s-katada/kobu/case/stl/main-unit/main-side-plate.stl

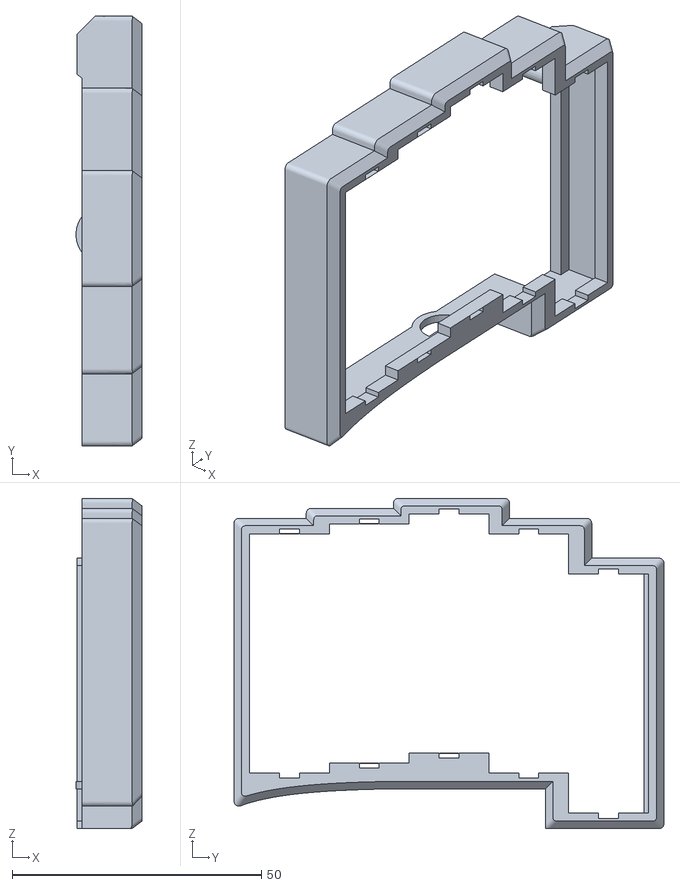
[picture p15: CAD file, 2026-05-27, an earlier design]
case/stl/main-unit/main-side-plate.stl
13.2 x 86.3 x 66.3
