s-katada/kobu/v1/case/3mf/08-main-top-plate.3mf

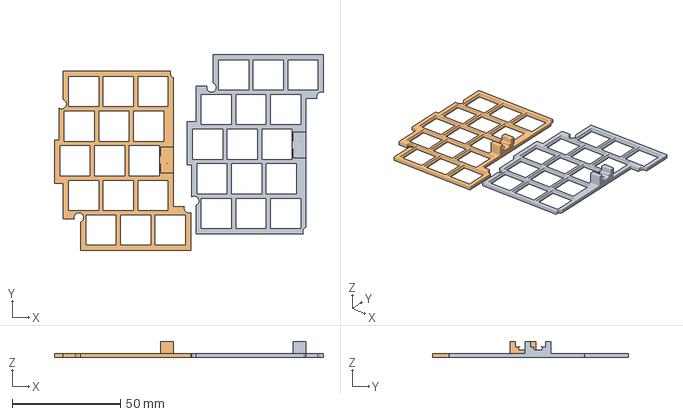
[picture p16: CAD file, 2026-07-02, an earlier design]
v1/case/3mf/08-main-top-plate.3mf
124.3 x 90.7 x 7.50 mm
main-top-plate-v1.stl x 2
