s-katada/kobu/v1/case/stl/main-unit/main-unit-left-spacer-top.stl

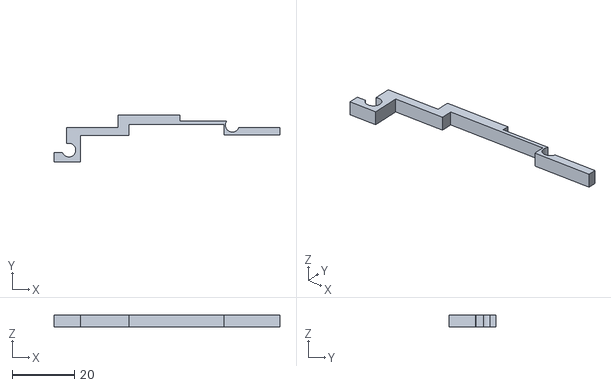
[picture p17: CAD file, 2026-07-02, an earlier design]
v1/case/stl/main-unit/main-unit-left-spacer-top.stl
72.5 x 15.1 x 3.90
