s-katada/kobu/v1/pcb/dxf/main-unit.dxf

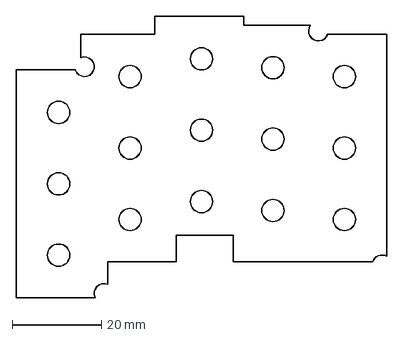
[picture p18: CAD file, 2026-07-02, an earlier design]
v1/pcb/dxf/main-unit.dxf
83.0 x 63.0 mm
