s-katada/kobu/v2/firmware/rmk/build.rs

use const_gen::*;
use std::fs::File;
use std::io::{Read, Write};
use std::path::{Path, PathBuf};
use std::{env, fs};
use xz2::read::XzEncoder;

fn main() {
    println!("cargo:rerun-if-changed=vial.json");
    println!("cargo:rerun-if-changed=keyboard.toml");

    patch_rmk_ble_for_macos();
    patch_rmk_battery_service();
    patch_rmk_battery_processor_signal();
    patch_rmk_battery_kobu_atomics();
    patch_rmk_kobu_settings_atomics();
    patch_rmk_via_custom_get_kobu();
    // NOTE: peripheral_bootloader_jump must run BEFORE via_custom_set_kobu_settings:
    // the latter anchors on the CustomSetValue arm AFTER the bootloader-jump patch
    // has rewritten the upstream stub. (Order only matters on a pristine registry —
    // e.g. a clean cargo cache or CI — because the patches are marker-idempotent.)
    patch_rmk_peripheral_bootloader_jump();
    patch_rmk_via_custom_set_kobu_settings();
    patch_rmk_via_custom_save_kobu();
    patch_rmk_macro_adc_acquisition_time();
    patch_rmk_host_advertise_fast();
    patch_rmk_split_peripheral_advertise_fast();
    patch_rmk_split_peripheral_wake_on_pointer();
    patch_rmk_split_peripheral_publish_battery();
    patch_rmk_split_peripheral_decode_battery_while_advertising();
    patch_rmk_conn_params_fast_settling();
    patch_rmk_host_conn_low_latency();
    patch_rmk_split_conn_low_latency();
    patch_rmk_split_conn_event_length();
    patch_rmk_split_conn_event_min_reservation();
    patch_rmk_split_conn_offbeat_interval();
    patch_rmk_macro_sdc_buffers();
    patch_rmk_flow_tap_exempt_language();
    patch_rmk_flow_tap_exempt_language_held();
    patch_rmk_split_state_resync_fast();
    patch_rmk_force_ble_conn_type();
    patch_rmk_force_hid_cccd_on_connect();
    patch_rmk_gate_ble_writer_on_encrypted();
    patch_rmk_timeout_ble_writer();
    patch_rmk_request_security_on_connect();
    patch_rmk_keymap_layer_pub();
    patch_rmk_last_key_tick_atomic();
    patch_rmk_record_last_key_tick();
    // Round 7 — boot-trackball BLE wedge + mouse-drag/copy. These add NEW
    // atomics and NEW rmk patches, so a `cargo clean --release -p rmk` is
    // required once after pulling this change (see the buildrs-patch-recompile
    // note in project memory). The atomics injection MUST run before the
    // patches that reference the atomics by path are compiled, but ordering
    // among build.rs functions only matters for anchor availability — so the
    // atomics patch anchors on the last-key-tick atomic injected just above.
    patch_rmk_kobu_wedge_drag_atomics();
    patch_rmk_set_host_connected();
    patch_rmk_timeout_split_writes();
    patch_rmk_capture_mouse_buttons();
    patch_rmk_pmw3610_slower_poll();
    // Round 8 — the boot-trackball wedge (R1–R7 all failed). Root cause: the
    // peripheral forwards every pointer sample over the split link with an
    // UNBOUNDED blocking write (split/peripheral.rs), flooding the central's
    // single shared trouBLE RX pool during the Mac SMP/encryption window and
    // silently dropping the encryption PDU → "connected but dead until a
    // supervision-timeout reconnect." Fix: bound that forward (Layer A) AND gate
    // the whole PMW3610 pipeline on BOTH halves until the host link is READY
    // (BLE-encrypted OR USB) — Layer B. Adds new atomics + a new SplitMessage
    // variant; REQUIRES `cargo clean --release -p rmk` (registry-patch gotcha).
    patch_rmk_kobu_input_gate_atomics();
    patch_rmk_timeout_peripheral_event_write();
    patch_rmk_pmw3610_input_gate();
    // Round 7 ball-diag atomics: must run before the two patches below, which
    // reference them (KOBU_BALL_FF_REJECTS / KOBU_BALL_INIT_READY).
    patch_rmk_kobu_ball_diag_atomics();
    // PMW3610 boot-lottery fix: the stock driver gives up after 3 init
    // attempts (~300 ms) and parks dead until power-cycle, and treats a
    // flaky-SPI all-0xff burst read as a real (phantom) motion sample.
    // Retry init forever (fast then relaxed backoff) and reject 0xff frames.
    patch_rmk_pmw3610_init_retry_forever();
    patch_rmk_pmw3610_reject_ff_frame();
    // Round 7 — scroll-death recurrence, no self-heal: a torn bit-banged SPI
    // config write (preempted mid-byte by MPSL radio interrupts) can leave
    // the sensor misconfigured but still Ready. Verify-and-retry the writes.
    patch_rmk_pmw3610_verify_init_writes();
    // Round 8 — live-confirmed (led-ball-diag): init retries fail while the
    // radio is busy, succeeding only in quiet moments. Run the one-time init
    // BEFORE the input gate (power-on is the reliably radio-quiet window).
    patch_rmk_pmw3610_early_init();
    // KOBU: patch_rmk_bitbang_atomic_bytes REVERTED 2026-07-15 (round 9) — a
    // mid-session central reboot (LED green/blue -> solid RED with scroll
    // dead, right ball fine; init_state can only reach that state via a
    // fresh boot + persistently-failing re-init) is suspected to be MPSL
    // tripping its interrupt-latency assert on the repeated ~30 µs PRIMASK
    // masks (7-byte bursts every 8 ms poll = constant masking). It also
    // couldn't protect the preemptible inter-byte Timer::after gaps, so it
    // was an incomplete fix regardless. Do NOT re-add without addressing
    // both: a latency budget that satisfies MPSL, and inter-byte coverage.
    patch_rmk_split_host_ready_variant();
    patch_rmk_emit_host_ready();
    patch_rmk_peripheral_apply_host_ready();
    // Round 10 — the wedge is a HANG (not reset) on the BONDED-RECONNECT-while-
    // Mac-holds-a-STALE-link path + trackball motion. On a stale resume the Mac
    // re-encrypts from the stored LTK and fires a dense GATT cache-revalidation
    // burst; kobu opened the trackball gate on the first encrypted GATT read
    // (R8), i.e. straight into that burst, BEFORE host TX credits were flowing —
    // the ~500Hz pointer flood then starved the single shared trouBLE TX queue +
    // 16-packet pool, the lone TxRunner parked on a host PDU, and the UNBOUNDED
    // `reply.send().await` in gatt_events_task deadlocked. Layer A bounds that
    // await; Layer C shrinks the stale window (5s->2s) like ZMK/KobitoKey.
    // (Layer B = a 2s post-encryption settle in run_input_gate_central, firmware;
    //  Layer D = bigger trouBLE pool via .cargo/config.toml env.)
    patch_rmk_timeout_gatt_reply();
    patch_rmk_supervision_timeout_2s();
    // Pointer "もっさり over time": macOS relaxes the bonded HID link to a slow
    // interval (~30-50ms) for power-saving after a while; rmk only logs the
    // change, so the pointer report rate drifts to ~20-33Hz and STAYS there
    // until reconnect. Capture the live interval and re-assert the fast 7.5ms
    // params, but only when actually drifted slow (don't spam macOS).
    patch_rmk_host_conn_interval_atomic();
    patch_rmk_reassert_fast_conn_params();
    // Round 12: make the round-11 re-assert EVENT-DRIVEN. After a motion-heavy
    // stale reconnect macOS lands the link fully relaxed (~30-50ms); the 10s
    // poll then took up to ~10s to pull it back to 7.5ms = the acute "もっさり→
    // しばらくで回復". Signal the re-assert loop the instant a slow interval lands
    // (in the ConnectionParamsUpdated arm) + keep a 2s backstop, collapsing the
    // recovery from ~10s to ms. Anchors on the round-11 patched text → run after.
    patch_rmk_conn_drift_atomic();
    patch_rmk_conn_drift_event_driven();
    // Round 18 — pointer もっさり OVER TIME = the macOS host link relaxes over a
    // session. kobu's stage-2 request was a FIXED min==max=7.5ms, BELOW Apple's
    // ~11.25ms BLE-HID floor → macOS SILENTLY REJECTS it → the link sits at
    // stage-1's fixed 15ms (66Hz, never the 7.5ms/133Hz ZMK reaches) and over
    // time relaxes into the 15-18ms band that the >18ms re-assert gate never
    // corrects. ZMK requests a RANGE 7.5-15ms (MIN_INT=6/MAX_INT=12) which macOS
    // CAN satisfy near its floor and HOLDS all session. This patch makes kobu
    // ZMK-faithful: stage-2 → range 7.5-15ms, re-assert → range 7.5-15ms, both
    // drift gates 18ms→12ms (close the dead band; matches the "past 12ms"
    // comment). ADDITIVE — anchors on the reassert/conn-drift patched text, so
    // it MUST run after them. Host-only + request-not-force → no wedge risk.
    patch_rmk_host_conn_range_zmk();
    // Round 19 — residual over-time excursions: macOS grants the MAX end of the
    // requested range, so round-18's [7.5,15ms] rested at 15ms (66Hz) and 15ms
    // ALSO tripped the >12ms gate (self-sustained re-assert churn that re-opens
    // negotiation → macOS re-grants the slow end). ZMK requests its range ONCE
    // and never perturbs it. Cap MAX at the 11.25ms Apple HID floor (rest
    // 89-133Hz) + raise the gate 12ms→13ms so the healthy point stops re-tripping
    // (a true relax ≥30ms still fires). ADDITIVE on the round-18 output → after.
    patch_rmk_host_conn_narrow_max_r19();
    // Round 21 — pointer のろのろ ROOT CAUSE (LED-confirmed: PURPLE ~15ms during
    // のろのろ, no white): peripheral LATENCY, not interval. kobu requested
    // max_latency=0 at every host conn-param site; ZMK requests latency=30.
    // latency=0 forbids macOS the cheap power-save (skip idle intervals), so its
    // ONLY lever is to RELAX THE INTERVAL (~15ms=66Hz=のろのろ); the 2s re-assert
    // then claws it back = the ~5s relax/recover loop. latency=30 keeps the fast
    // interval and lets macOS skip idle events instead (ZMK behaviour). Host conn
    // only (the split link in split/ble/central.rs stays latency 0 — low relay
    // lag). Active input is instant (latency applies only when idle).
    patch_rmk_host_latency_30_r21();
    // Round 23 diagnostic — count pointer samples PRODUCED by the PMW3610 (in
    // read_event) so the PERIPHERAL LED can show its own production rate. The
    // central LED already shows the ARRIVAL rate; comparing the two decisively
    // separates "right sensor produces too few" (production) from "split link
    // loses them in transit". Two additive patches (atomic + increment).
    patch_rmk_peripheral_samples_atomic_r23();
    patch_rmk_peripheral_samples_count_r23();
    // Round 24 — のろのろ ROOT CAUSE (confirmed: both diag LEDs green during のろのろ
    // ⇒ samples reach the central fine; host link is the issue; "~5s recovery" =
    // kobu's 2s re-assert cycle). kobu RE-ASSERTS host conn-params every 2s
    // (churn), which re-opens negotiation and makes macOS RELAX the link →
    // のろのろ → re-assert claws back in ~5s → relaxes again. KobitoKey requests
    // host params ONCE ([7.5,15ms], latency 0, sup 2s) and never touches them, so
    // macOS HOLDS the link = smooth. Make kobu KobitoKey-exact + REQUEST-ONCE:
    // latency 30→0, max 11.25→15ms ([7.5,15] range macOS accepts & holds), and
    // neuter both re-assert gates (>13ms → >4s = never fires) so no churn.
    patch_rmk_host_conn_request_once_r24();
    // Round 25 — pointer-triggered host conn refresh v2 (port of the previously
    // REGISTRY-ONLY hand patch the flashed UF2s were built from). R24's
    // request-once killed the churn but removed every recovery path: once macOS
    // power-relaxes the bonded link (~15ms → 30-50ms after an idle spell),
    // nothing pulls it back. Keep request-once for the healthy/idle case, but
    // turn the old re-assert loop into a pure consumer of KOBU_HOST_CONN_DRIFT:
    // no periodic backstop (the 2s select backstop is dropped), gate restored
    // to the >12ms fast-HID-band edge; the signal is fired by kobu's
    // PointerProcessor (src/trackball.rs) only during ACTIVE ball motion,
    // cooldown-limited. Anchors on the R12 select-backstop loop as rewritten by
    // R18/R19/R24, so it MUST run AFTER patch_rmk_host_conn_request_once_r24
    // (and no later ble/mod.rs patch may come between them, keeping the
    // appended marker order — and therefore the file bytes — exact).
    patch_rmk_host_conn_refresh_r25();
    // Fast bring-up (2026-07-13): latch KOBU_HOST_CONNECTED on the
    // ConnectionParamsUpdated arm (encrypted-link check inline) instead of
    // waiting on a GATT READ a cache-warm bonded reconnect may send late or
    // never. Must be the LAST ble/mod.rs patch (anchors on round-11 text).
    patch_rmk_host_connected_on_params_update();

    // Round 26 — pointer のろのろ TRUE ROOT CAUSE = the i8 (±127) mouse report.
    // RMK's mouse HID report is i8 x/y and kobu emits ONE report per BLE
    // connection event (the len()==0 gate), so the maximum deliverable cursor
    // speed is host_rate × 127 counts/s ≈ 24 cm/s at the measured ~15ms link.
    // Roll faster and the excess is dropped at the pend clamp → the cursor
    // under-travels = のろのろ. ZMK uses 16-bit (±32767) motion so ONE report
    // per interval carries the full coalesced delta and there is no speed
    // ceiling. These patches widen RMK's mouse motion to i16 (ZMK parity):
    //   - descriptor.rs: CompositeReport x/y i8→i16 (report map 111→121 bytes)
    //   - hid.rs: add Report::MouseReportWide(WheelMouseReport) (16-bit payload)
    //   - ble_server.rs: mouse characteristic [u8;5]→[u8;7], report_map [u8;121],
    //     widen the legacy i8 MouseReport arm + add the wide arm (both → 7 bytes)
    //   - usb/mod.rs: same widening on the USB composite mouse report
    // kobu's PointerProcessor (trackball.rs) emits MouseReportWide; the i8 path
    // (keyboard mouse-buttons, scroll wheel, unused rmk processors) is widened
    // at the serializer so every payload to the now-7-byte characteristic is
    // byte-consistent with the 16-bit report map. Anchors are pristine text →
    // order-independent. Changing the report map REQUIRES the host (macOS) to
    // re-pair. REQUIRES `cargo clean --release -p rmk` (registry-patch gotcha).
    patch_rmk_descriptor_mouse_i16();
    patch_rmk_hid_mouse_wide_variant();
    patch_rmk_ble_server_mouse_i16();
    patch_rmk_usb_mouse_i16();

    // Step 2 (RMK fix series) — ZMK-parity PPCP (0x2A04). macOS relaxes the
    // bonded host link to ~30-50ms when idle; ZMK keyboards stay in-band
    // because they EXPOSE the Peripheral Preferred Connection Parameters
    // characteristic in the GAP service (7.5ms/15ms/latency 0/timeout 2s) and
    // macOS reads it at (re)connect. trouble-host 0.5.1 has PPCP stubbed out
    // (src/gap.rs TODO), so this patches the trouble-host REGISTRY source —
    // the first build.rs patch outside the rmk crate. It also bumps
    // GAP_SERVICE_ATTRIBUTE_COUNT 6 -> 8, which auto-grows every bare
    // #[gatt_server] attribute table (rmk has three, all bare) so the
    // heapless push().unwrap() in trouble's attribute.rs can never overflow.
    // Anchors only on trouble-host text → order-independent of the rmk
    // patches above. REQUIRES `cargo clean --release -p trouble-host` once
    // (registry-patch gotcha, same as the TROUBLE_HOST_* envs in
    // .cargo/config.toml). Bonded Macs cache the GATT DB and trouble has no
    // Service Changed characteristic → unpair + re-pair to actually see PPCP
    // (precedent: the 2026-05-15 BAS addition).
    patch_trouble_gap_ppcp();

    // :/; final round (2026-06-12) — host truth: the Mac's Karabiner-Elements
    // "Exchange semicolon and colon" rule (no device filter) inverts ; and :
    // for EVERY keyboard, so the firmware emits NORMAL US semantics and the
    // host rule does the swap (see keyboard.toml [behavior.morse] notes).
    // Patch 1 makes the Shift+';' chord resolve at the PRESS edge like a real
    // keyboard (rmk otherwise emits morse taps at release time with that
    // instant's modifiers — the era-P fast-chord failure). Patch 2 turns the
    // clearlayout ritual into a FULL config resync: Vial-written combo/fork/
    // morse/macro flash slots previously survived every reset and were
    // overlaid over keyboard.toml at boot (fill_vec pads to capacity, then
    // read_* overwrite per index). Both anchor on PRISTINE files
    // (keyboard/morse.rs, storage/mod.rs — no other kobu patch touches them)
    // — order-independent. NEW registry patches ⇒ one
    // `cargo clean --release -p rmk` before the next build (R7/R8 gotcha).
    patch_rmk_morse_shift_chord_instant_tap();
    patch_rmk_colon_native_invert();
    patch_rmk_colon_chord_combo_aware();
    patch_rmk_flow_tapped_space_language_rescue();
    patch_rmk_colon_mask_own_report();
    patch_rmk_flow_tap_exempt_layer_taps();
    patch_rmk_normal_mode_buffering();
    patch_rmk_kana_press_edge();
    // D+F combo → WM(No, ⌘⌥) chord fix: rmk's anti-leak clear kills any
    // pure modifier hold on the next keypress, so ⌘⌥+Space never chorded.
    // Flag pure holds (KeyCode::No) and skip the clear while one is active.
    patch_rmk_pure_wm_hold_chord();
    patch_rmk_enter_chord_press_edge();
    patch_rmk_clearlayout_resync_vial_tables();
    // Fast bring-up (round 4): give Storage a shared KeyPointerCache so boot
    // reads stop doing 300+ NoCache full-map linear scans once the map is
    // dirty with months of Vial/settings/bond appends (storage-wipe test
    // confirmed this is the dominant remaining boot cost). Must run after
    // clearlayout_resync_vial_tables (anchors on its reset_layout_only tail).
    patch_rmk_storage_boot_cache();
    // クリック救済 (2026-06-12) — "ほぼ静止しないとクリックできない / 微調整中に
    // レイヤーが切れる". Inject KOBU_LAST_TYPING_TICKS + KOBU_AUTO_MOUSE_LAYER
    // and stamp the typing tick in KeyMap::get_action_with_layer_cache when a
    // press falls THROUGH a transparent auto-mouse-layer slot (and isn't a bare
    // modifier) — i.e. the user resumed typing while mousing. The firmware hold
    // loop (src/trackball.rs) polls it to drop layer 4 instantly, which is what
    // lets the idle timeout be a click-friendly 600 ms. Statics anchor on the
    // KOBU_MOUSE_BUTTONS line (injected by patch_rmk_kobu_wedge_drag_atomics →
    // must run after it); the keymap.rs anchor is pristine text. NEW registry
    // patch ⇒ one `cargo clean --release -p rmk` before the next build.
    patch_rmk_typing_tick();
    // Linux layer yield (2026-08-26): kobu2's Linux OS layer is index 7 — the
    // TOP of the stack — but semantically it must rank just above BASE (it
    // only exists to give H the Ctrl+H→Backspace fork token). Without this,
    // its H slot shadowed every momentary layer's H position while the Linux
    // toggle was latched: Space-layer ← (layer 2 H), settings F6, Emacs
    // Backspace, and the auto-mouse transparent H all resolved to TD(3)
    // instead (user report: 「super+tabでアプリを切り替えるときに左矢印が
    // 効かない」). Runtime-inert for v1 (its NUM_LAYER is 7, so layer index 7
    // never iterates). NEW registry patch ⇒ one `cargo clean --release -p rmk`
    // before the next build.
    patch_rmk_linux_layer_yield();
    // Buffered-morse-follower re-resolve (2026-08-26): follow-up to
    // patch_rmk_linux_layer_yield — that patch only helps resolutions that
    // happen AFTER the momentary layer latches. A follower pressed inside a
    // tap-hold's undecided window is buffered with its action FROZEN at
    // arrival time (keyboard.rs Buffer arm); when the hold wins by TIMEOUT,
    // non-morse followers are repaired by fire_held_non_morse_keys' by-
    // position re-resolve, but a follower whose stale action is itself MORSE
    // (layer 7's H slot = TD(3) fork token, resolved before layer 2 latched)
    // is skipped by that flush AND blocks it via the Pressed-morse early
    // return — so the FIRST Space-layer ← after latching the Linux layer
    // emitted the TD(3) tap 'h' (host saw Super+H, switcher didn't move);
    // presses 2+ worked. Fix: right after a morse-timeout resolution,
    // re-resolve still-Pressed morse followers against the now-current layer
    // state. Gated on NUM_LAYER > 7 ⇒ compile-time inert for v1 (NUM_LAYER
    // 7). NEW registry patch ⇒ one `cargo clean --release -p rmk` before the
    // next build.
    patch_rmk_morse_follower_reresolve();

    // Dongle topology (Prospector, 2026-08): the ONE registry hook that lets a
    // 2-peripheral dongle central tell its halves apart (rmk strips the
    // peripheral id before re-injecting forwarded events), plus a wider
    // connect timeout so two peripheral managers sharing SCANNING_MUTEX don't
    // clear each other's stored addresses at cold boot. Both patches are
    // runtime-inert for the classic left-central topology: the id-gated branch
    // only fires for id != 0 and the classic build's only peripheral is id 0.
    // NEW registry patches ⇒ one `cargo clean --release -p rmk` first.
    patch_rmk_peripheral_manager_source_disambiguation();
    patch_rmk_split_connect_timeout_widen();
    patch_rmk_split_adv_set_token();

    // USB/BLE endpoint arbitration (2026-08-18): "BLE でつないだまま有線に挿すと
    // 入力できない" の修正。rmk-0.8.2 は接続先をループ先頭で一度しか決めず、BLE
    // が接続した瞬間に USB キーボード future を捨てるので、有線側は列挙される
    // だけでレポートが 1 本も出ない。part 1 は usb/mod.rs に ZMK の
    // `zmk_usb_is_hid_ready()` 相当のフラグを、part 2 は ble/mod.rs の
    // BLE-priority ブランチに「有線ホストが来たら乗り換える / 抜けたら戻る」を
    // 入れる。NEW registry patches ⇒ one `cargo clean --release -p rmk` first.
    patch_rmk_usb_hid_ready_flag();
    patch_rmk_usb_takes_over_ble();
    // 2026-09-08 — travel-conserving split forward. Round 8 Layer A bounded the
    // peripheral's pointer forward to 20 ms but `let _ =` DISCARDED the sample
    // that missed it; a host-side HID capture (IOHIDManager, this Mac) measured
    // ~12% of right-ball samples lost in fast motion with NO catch-up in the
    // next report = the "もっさり" under-travel. Carry the dropped X/Y counts
    // into the next pointer sample instead, and count carries. Anchors on the
    // round-7/round-8 patched text, so both must run after
    // patch_rmk_kobu_ball_diag_atomics and patch_rmk_timeout_peripheral_event_write.
    // NEW rmk registry patches: `cargo clean --release -p rmk` once after pulling.
    patch_rmk_kobu_forward_carry_atomics();
    patch_rmk_peripheral_forward_carry();
    // 2026-09-08 — central-side LOSS LEDGER + the stale-assumption fix it found.
    // ble_server.rs bounds the mouse notify at 40 ms and `return Ok(0)` on
    // timeout; its justification ("run_pointer_flush re-emits motion from its
    // accumulator") is STALE — that task is gone and PointerProcessor already
    // deducted the travel from pend_* when it handed the report over, so a
    // timeout silently ate it. Hand the travel back and count every stage so
    // the Mac can read a full ledger over Via 0xC0 (ids 0x20-0x28).
    // NEW rmk registry patches: `cargo clean --release -p rmk` once.
    patch_rmk_kobu_loss_ledger_atomics();
    patch_rmk_hid_writer_drop_carry();
    patch_rmk_central_event_drop_count();
    patch_rmk_via_custom_get_loss_ledger();
    // 2026-09-10 — status-LED BLE feedback. A BONDED reconnect re-encrypts
    // from the stored LTK and raises no PairingComplete, so rmk's `connected`
    // flag stayed false and `ControllerEvent::BleState(_, Connected)` was
    // never published: the new waiting-blink would have blinked straight
    // through a live link. Set the flag in the round-7 encryption arm too.
    // Anchors on patch_rmk_set_host_connected's text, so it must run after.
    patch_rmk_publish_connected_on_bonded_reconnect();

    // H+J hold → peripheral (right) trackball as scroll (2026-09-15). Combo
    // emits User15 while held; process_user latches KOBU_PERIPH_AS_SCROLL;
    // PeriphScrollRelabel (src/trackball.rs) rewrites X/Y → H/V so
    // ScrollProcessor claims the right ball until release. NEW registry
    // patches ⇒ one `cargo clean --release -p rmk` before the next build.
    patch_rmk_periph_scroll_hold_atomic();
    patch_rmk_periph_scroll_hold_user15();

    generate_vial_config();

    let out = &PathBuf::from(env::var_os("OUT_DIR").unwrap());
    File::create(out.join("memory.x"))
        .unwrap()
        .write_all(include_bytes!("memory.x"))
        .unwrap();
    println!("cargo:rustc-link-search={}", out.display());

    println!("cargo:rerun-if-changed=memory.x");

    println!("cargo:rustc-link-arg=--nmagic");
    println!("cargo:rustc-link-arg=-Tlink.x");
    println!("cargo:rustc-link-arg=-Tdefmt.x");

    println!("cargo:rustc-linker=flip-link");
}

/// Round 26 (mouse-i16, part 1/4): widen `CompositeReport` mouse x/y from i8 to
/// i16 in the rmk HID report map, and append a 7-byte `WheelMouseReport` wire
/// payload struct. `CompositeReport::desc()` then declares 16-bit relative X/Y
/// (REPORT_SIZE 16, logical ±32767) and grows 111 -> 121 bytes (host-verified).
fn patch_rmk_descriptor_mouse_i16() {
    const MARKER: &str = "// kobu: CompositeReport mouse x/y widened i8 -> i16 + WheelMouseReport applied";
    const RMK_VERSION: &str = "0.8.2";
    let Some(path) = find_rmk_file(RMK_VERSION, "src/descriptor.rs") else {
        println!(
            "cargo:warning=kobu: could not find rmk-{RMK_VERSION} descriptor.rs; mouse-i16 descriptor patch not applied"
        );
        return;
    };
    println!("cargo:rerun-if-changed={}", path.display());
    let mut contents = fs::read_to_string(&path)
        .unwrap_or_else(|e| panic!("kobu: failed to read {}: {e}", path.display()));
    if contents.contains(MARKER) {
        return;
    }
    let x_from = "    pub(crate) x: i8,";
    let y_from = "    pub(crate) y: i8,";
    if !contents.contains(x_from) || !contents.contains(y_from) {
        panic!(
            "kobu: expected rmk-{RMK_VERSION} descriptor.rs CompositeReport x/y i8 fields missing in {}; \
             upstream changed — update firmware/build.rs::patch_rmk_descriptor_mouse_i16",
            path.display()
        );
    }
    contents = contents.replace(x_from, "    pub(crate) x: i16,");
    contents = contents.replace(y_from, "    pub(crate) y: i16,");
    let wheel_struct = r#"

/// kobu: 16-bit relative mouse motion wire payload (7 bytes: buttons + i16 x +
/// i16 y + i8 wheel + i8 pan). ssmarshal serializes it little-endian/packed to
/// exactly 7 bytes, matching the report_id 0x01 (mouse) section of
/// `CompositeReport` once its x/y are widened to i16 above — so the report map
/// (`CompositeReport::desc()`) and this payload stay byte-consistent.
#[derive(Clone, Copy, Debug, Default, Serialize)]
pub struct WheelMouseReport {
    pub buttons: u8,
    pub x: i16,
    pub y: i16,
    pub wheel: i8,
    pub pan: i8,
}
"#;
    contents.push_str(wheel_struct);
    contents.push('\n');
    contents.push_str(MARKER);
    contents.push('\n');
    fs::write(&path, contents)
        .unwrap_or_else(|e| panic!("kobu: failed to write {}: {e}", path.display()));
}

/// Round 26 (mouse-i16, part 2/4): add a `Report::MouseReportWide` enum variant
/// carrying the 16-bit `WheelMouseReport`. kobu's PointerProcessor emits this;
/// the legacy `MouseReport` (i8) variant is kept for mouse-buttons / scroll /
/// unused rmk processors and widened at the serializer.
fn patch_rmk_hid_mouse_wide_variant() {
    const MARKER: &str = "// kobu: Report::MouseReportWide 16-bit variant applied";
    const RMK_VERSION: &str = "0.8.2";
    let Some(path) = find_rmk_file(RMK_VERSION, "src/hid.rs") else {
        println!(
            "cargo:warning=kobu: could not find rmk-{RMK_VERSION} hid.rs; mouse-wide variant patch not applied"
        );
        return;
    };
    println!("cargo:rerun-if-changed={}", path.display());
    let mut contents = fs::read_to_string(&path)
        .unwrap_or_else(|e| panic!("kobu: failed to read {}: {e}", path.display()));
    if contents.contains(MARKER) {
        return;
    }
    let from = "    /// Mouse hid report\n    MouseReport(MouseReport),";
    let to = "    /// Mouse hid report\n    MouseReport(MouseReport),\n    /// kobu: high-resolution 16-bit relative mouse motion report\n    MouseReportWide(crate::descriptor::WheelMouseReport),";
    if !contents.contains(from) {
        panic!(
            "kobu: expected rmk-{RMK_VERSION} hid.rs Report::MouseReport variant missing in {}; \
             upstream changed — update firmware/build.rs::patch_rmk_hid_mouse_wide_variant",
            path.display()
        );
    }
    contents = contents.replace(from, to);
    contents.push('\n');
    contents.push_str(MARKER);
    contents.push('\n');
    fs::write(&path, contents)
        .unwrap_or_else(|e| panic!("kobu: failed to write {}: {e}", path.display()));
}

/// Round 26 (mouse-i16, part 3/4): the BLE composite mouse characteristic.
/// Report map 111 -> 121 bytes, mouse value [u8;5] -> [u8;7], widen the legacy
/// i8 `MouseReport` write arm to the 7-byte payload, and add the wide arm.
fn patch_rmk_ble_server_mouse_i16() {
    const MARKER: &str = "// kobu: BLE mouse characteristic widened to i16 (7-byte) applied";
    const RMK_VERSION: &str = "0.8.2";
    let Some(path) = find_rmk_file(RMK_VERSION, "src/ble/ble_server.rs") else {
        println!(
            "cargo:warning=kobu: could not find rmk-{RMK_VERSION} ble_server.rs; mouse-i16 ble patch not applied"
        );
        return;
    };
    println!("cargo:rerun-if-changed={}", path.display());
    let mut contents = fs::read_to_string(&path)
        .unwrap_or_else(|e| panic!("kobu: failed to read {}: {e}", path.display()));
    if contents.contains(MARKER) {
        return;
    }
    let rm_msg_from = "expect(\"Failed to convert CompositeReport to [u8; 111]\")";
    let rm_field_from = "    pub(crate) report_map: [u8; 111],";
    let char_field_from = "    pub(crate) mouse_report: [u8; 5],";
    let char_handle_from = "    pub(crate) mouse_report: Characteristic<[u8; 5]>,";
    let arm_from = "                let mut buf = [0u8; 5];\n                let n = serialize(&mut buf, &mouse_report).map_err(|_| HidError::ReportSerializeError)?;";
    let wide_arm_anchor = "            Report::MediaKeyboardReport(media_keyboard_report) => {";
    for frag in [
        rm_msg_from,
        rm_field_from,
        char_field_from,
        char_handle_from,
        arm_from,
        wide_arm_anchor,
    ] {
        if !contents.contains(frag) {
            panic!(
                "kobu: expected rmk-{RMK_VERSION} ble_server.rs anchor missing in {}: `{frag}`; \
                 upstream changed — update firmware/build.rs::patch_rmk_ble_server_mouse_i16",
                path.display()
            );
        }
    }
    contents = contents.replace(
        rm_msg_from,
        "expect(\"Failed to convert CompositeReport to [u8; 121]\")",
    );
    contents = contents.replace(rm_field_from, "    pub(crate) report_map: [u8; 121],");
    contents = contents.replace(char_field_from, "    pub(crate) mouse_report: [u8; 7],");
    contents = contents.replace(
        char_handle_from,
        "    pub(crate) mouse_report: Characteristic<[u8; 7]>,",
    );
    contents = contents.replace(
        arm_from,
        "                let mut buf = [0u8; 7];\n                let __wide = crate::descriptor::WheelMouseReport {\n                    buttons: mouse_report.buttons,\n                    x: mouse_report.x as i16,\n                    y: mouse_report.y as i16,\n                    wheel: mouse_report.wheel,\n                    pan: mouse_report.pan,\n                };\n                let n = serialize(&mut buf, &__wide).map_err(|_| HidError::ReportSerializeError)?;",
    );
    contents = contents.replace(
        wide_arm_anchor,
        "            Report::MouseReportWide(mouse_report) => {\n                let mut buf = [0u8; 7];\n                let n = serialize(&mut buf, &mouse_report).map_err(|_| HidError::ReportSerializeError)?;\n                match ::embassy_time::with_timeout(\n                    ::embassy_time::Duration::from_millis(40),\n                    self.mouse_report.notify(self.conn, &buf),\n                )\n                .await\n                {\n                    Ok(r) => r.map_err(|e| {\n                        error!(\"Failed to notify wide mouse report: {:?}\", e);\n                        HidError::BleError\n                    })?,\n                    Err(_) => return Ok(0),\n                };\n                Ok(n)\n            }\n            Report::MediaKeyboardReport(media_keyboard_report) => {",
    );
    contents.push('\n');
    contents.push_str(MARKER);
    contents.push('\n');
    fs::write(&path, contents)
        .unwrap_or_else(|e| panic!("kobu: failed to write {}: {e}", path.display()));
}

/// Round 26 (mouse-i16, part 4/4): the USB composite mouse path. Widen the
/// legacy i8 mouse arm to the 7-byte payload and add the wide arm, so a wired
/// session stays byte-consistent with the now-16-bit report map.
fn patch_rmk_usb_mouse_i16() {
    const MARKER: &str = "// kobu: USB composite mouse widened to i16 (7-byte) applied";
    const RMK_VERSION: &str = "0.8.2";
    let Some(path) = find_rmk_file(RMK_VERSION, "src/usb/mod.rs") else {
        println!(
            "cargo:warning=kobu: could not find rmk-{RMK_VERSION} usb/mod.rs; mouse-i16 usb patch not applied"
        );
        return;
    };
    println!("cargo:rerun-if-changed={}", path.display());
    let mut contents = fs::read_to_string(&path)
        .unwrap_or_else(|e| panic!("kobu: failed to read {}: {e}", path.display()));
    if contents.contains(MARKER) {
        return;
    }
    let arm_from = "                let n = serialize(&mut buf[1..], &mouse_report).map_err(|_| HidError::ReportSerializeError)?;";
    let wide_arm_anchor = "            Report::MediaKeyboardReport(media_keyboard_report) => {";
    if !contents.contains(arm_from) || !contents.contains(wide_arm_anchor) {
        panic!(
            "kobu: expected rmk-{RMK_VERSION} usb/mod.rs mouse arm anchors missing in {}; \
             upstream changed — update firmware/build.rs::patch_rmk_usb_mouse_i16",
            path.display()
        );
    }
    contents = contents.replace(
        arm_from,
        "                let __wide = crate::descriptor::WheelMouseReport {\n                    buttons: mouse_report.buttons,\n                    x: mouse_report.x as i16,\n                    y: mouse_report.y as i16,\n                    wheel: mouse_report.wheel,\n                    pan: mouse_report.pan,\n                };\n                let n = serialize(&mut buf[1..], &__wide).map_err(|_| HidError::ReportSerializeError)?;",
    );
    contents = contents.replace(
        wide_arm_anchor,
        "            Report::MouseReportWide(mouse_report) => {\n                let mut buf: [u8; 9] = [0; 9];\n                buf[0] = CompositeReportType::Mouse as u8;\n                let n = serialize(&mut buf[1..], &mouse_report).map_err(|_| HidError::ReportSerializeError)?;\n                self.other_writer\n                    .write(&buf[0..n + 1])\n                    .await\n                    .map_err(HidError::UsbEndpointError)?;\n                Ok(n)\n            }\n            Report::MediaKeyboardReport(media_keyboard_report) => {",
    );
    contents.push('\n');
    contents.push_str(MARKER);
    contents.push('\n');
    fs::write(&path, contents)
        .unwrap_or_else(|e| panic!("kobu: failed to write {}: {e}", path.display()));
}

fn generate_vial_config() {
    let out_file = Path::new(&env::var_os("OUT_DIR").unwrap()).join("config_generated.rs");

    let p = Path::new("vial.json");
    let mut content = String::new();
    match File::open(p) {
        Ok(mut file) => {
            file.read_to_string(&mut content)
                .expect("Cannot read vial.json");
        }
        Err(e) => println!("Cannot find vial.json {:?}: {}", p, e),
    };

    let vial_cfg = json::stringify(json::parse(&content).unwrap());
    let mut keyboard_def_compressed: Vec<u8> = Vec::new();
    XzEncoder::new(vial_cfg.as_bytes(), 6)
        .read_to_end(&mut keyboard_def_compressed)
        .unwrap();

    let keyboard_id: Vec<u8> = vec![0xB9, 0xBC, 0x09, 0xB2, 0x9D, 0x37, 0x4C, 0xEA];
    let const_declarations = [
        const_declaration!(pub VIAL_KEYBOARD_DEF = keyboard_def_compressed),
        const_declaration!(pub VIAL_KEYBOARD_ID = keyboard_id),
    ]
    .map(|s| "#[allow(clippy::redundant_static_lifetimes)]\n".to_owned() + s.as_str())
    .join("\n");
    fs::write(out_file, const_declarations).unwrap();
}

/// Apply small, idempotent patches to the crates.io `rmk` 0.8.2 sources.
///
/// 1. Advertise on LE 1M PHY — macOS Bluetooth settings often ignore peripherals
///    that only advertise on LE 2M (RMK hard-codes 2M in `advertise()`).
/// 2. Default to BLE-priority when no connection preference is stored — RMK 0.8
///    otherwise defaults to USB, which suppresses BLE discovery while USB is
///    attached (HaoboGu/rmk#157, #159).
fn patch_rmk_ble_for_macos() {
    const MARKER: &str = "// kobu: macOS BLE patches applied";
    const RMK_VERSION: &str = "0.8.2";

    let Some(path) = find_rmk_ble_mod(RMK_VERSION) else {
        println!(
            "cargo:warning=kobu: could not find rmk-{RMK_VERSION} in the cargo registry; \
             macOS BLE patches were not applied"
        );
        return;
    };

    println!("cargo:rerun-if-changed={}", path.display());

    let mut contents = fs::read_to_string(&path).unwrap_or_else(|e| {
        panic!("kobu: failed to read {}: {e}", path.display());
    });

    if contents.contains(MARKER) {
        return;
    }

    let replacements = [
        (
            "primary_phy: PhyKind::Le2M,\n        secondary_phy: PhyKind::Le2M,",
            "primary_phy: PhyKind::Le1M,\n        secondary_phy: PhyKind::Le1M,",
        ),
        (
            "CONNECTION_TYPE.store(ConnectionType::Usb.into(), Ordering::SeqCst);",
            "CONNECTION_TYPE.store(ConnectionType::Ble.into(), Ordering::SeqCst);",
        ),
    ];

    for (from, to) in replacements {
        if !contents.contains(from) {
            panic!(
                "kobu: expected rmk-{RMK_VERSION} source fragment missing in {}; \
                 upstream may have changed — update firmware/build.rs",
                path.display()
            );
        }
        contents = contents.replace(from, to);
    }

    contents.push('\n');
    contents.push_str(MARKER);
    contents.push('\n');

    fs::write(&path, contents).unwrap_or_else(|e| {
        panic!("kobu: failed to write {}: {e}", path.display());
    });
}

fn find_rmk_ble_mod(rmk_version: &str) -> Option<PathBuf> {
    find_rmk_file(rmk_version, "src/ble/mod.rs")
}

fn find_rmk_file(rmk_version: &str, rel_path: &str) -> Option<PathBuf> {
    let home = env::var("HOME")
        .or_else(|_| env::var("USERPROFILE"))
        .ok()?;
    let src_root = PathBuf::from(home).join(".cargo/registry/src");
    let entries = fs::read_dir(&src_root).ok()?;
    let crate_dir = format!("rmk-{rmk_version}");
    let rel = Path::new(&crate_dir).join(rel_path);

    for entry in entries.flatten() {
        let candidate = entry.path().join(&rel);
        if candidate.is_file() {
            return Some(candidate);
        }
    }
    None
}

/// Replace `rmk-0.8.2/src/ble/battery_service.rs` wholesale with a kobu-flavoured
/// version that:
///
/// 1. Adds the BAS 1.1 `Battery Level Status` characteristic (UUID `0x2BED`)
///    next to the legacy Battery Level so hosts that understand BAS 1.1 (macOS
///    Sequoia, iOS 17+) can render a charging icon next to the kobu's
///    percentage.
/// 2. Rewrites `BleBatteryServer::run` to push a sentinel value immediately
///    on connect (macOS won't surface a BAS reading of 0%), drop the upstream
///    keypress gate, and heartbeat both characteristics every ~10s so VBUS
///    plug/unplug events get reflected in the Bluetooth menu without waiting
///    for the user to type a key.
/// 3. Polls VBUS via `embassy_nrf::pac::POWER.usbregstatus().vbusdetect()` on
///    every loop iteration — kobu's central is the only place that knows the
///    USB-power state, and we don't want to pipe a separate signal through
///    just for this.
///
/// We replace the entire upstream `battery_service.rs` body because the
/// changes touch the `BatteryService` struct, the `BleBatteryServer` type,
/// the constructor, and the run loop simultaneously — a fragile multi-hunk
/// find/replace would force us to re-tune every time we tweak one piece.
fn patch_rmk_battery_service() {
    // Increment the version suffix every time the embedded payload changes.
    const MARKER: &str = "// kobu: battery_service v3 (BAS 1.1 + VBUS charging) applied";
    // Sentinel that must be present in upstream rmk-0.8.2 — if missing, the
    // crate has been reorganised and our overwrite would land on the wrong
    // file.
    const UPSTREAM_SENTINEL: &str = "use crate::input_device::battery::{BATTERY_UPDATE, BatteryState};";
    const RMK_VERSION: &str = "0.8.2";

    let Some(path) = find_rmk_file(RMK_VERSION, "src/ble/battery_service.rs") else {
        println!(
            "cargo:warning=kobu: could not find rmk-{RMK_VERSION} battery_service.rs; \
             v3 patch was not applied"
        );
        return;
    };

    println!("cargo:rerun-if-changed={}", path.display());

    let existing = fs::read_to_string(&path).unwrap_or_else(|e| {
        panic!("kobu: failed to read {}: {e}", path.display());
    });

    if existing.contains(MARKER) {
        return;
    }

    if !existing.contains(UPSTREAM_SENTINEL) {
        panic!(
            "kobu: expected rmk-{RMK_VERSION} battery_service.rs sentinel missing in {}; \
             upstream may have changed — update firmware/build.rs",
            path.display()
        );
    }

    let new_contents = r##"use embassy_time::Timer;
use trouble_host::prelude::*;

use super::ble_server::Server;
use crate::input_device::battery::{BATTERY_UPDATE, BatteryState};

/// Battery service — kobu v3 layout. Includes both the classic BAS 1.0
/// Battery Level (0x2A19) characteristic and the BAS 1.1 Battery Level
/// Status (0x2BED) characteristic so hosts that understand BAS 1.1 can
/// surface a charging icon alongside the percentage.
#[gatt_service(uuid = service::BATTERY)]
pub(crate) struct BatteryService {
    /// Battery Level — u8 percentage 0..=100.
    #[descriptor(uuid = descriptors::VALID_RANGE, read, value = [0, 100])]
    #[characteristic(uuid = characteristic::BATTERY_LEVEL, read, notify)]
    pub(crate) level: u8,

    /// Battery Level Status (BAS 1.1) — 3-byte payload.
    ///
    /// Byte 0: `flags` — kobu always sends 0 (no optional fields present;
    /// the battery level is carried by the legacy 0x2A19 characteristic
    /// rather than the BAS 1.1 in-band copy).
    ///
    /// Bytes 1..3: `power_state` as a little-endian u16 with the standard
    /// BAS 1.1 bit layout:
    ///
    ///   * bit 0      = battery present (always 1 — kobu has a LiPo).
    ///   * bits 1..2  = wired external power source. 00 = absent, 01 =
    ///                  present. We set 01 when VBUS is detected (USB
    ///                  plugged in).
    ///   * bits 3..4  = wireless external power source. Always 00.
    ///   * bits 5..6  = battery charge state. 00 = unknown,
    ///                  01 = charging, 10 = discharging-active,
    ///                  11 = discharging-inactive. kobu emits 01 when
    ///                  VBUS is present and 10 otherwise.
    ///   * bits 7..15 = unused / reserved bits — left zero.
    #[characteristic(uuid = characteristic::BATTERY_LEVEL_STATUS, read, notify)]
    pub(crate) level_status: [u8; 3],
}

pub(crate) struct BleBatteryServer<'stack, 'server, 'conn, P: PacketPool> {
    pub(crate) battery_level: Characteristic<u8>,
    pub(crate) battery_level_status: Characteristic<[u8; 3]>,
    pub(crate) conn: &'conn GattConnection<'stack, 'server, P>,
}

impl<'stack, 'server, 'conn, P: PacketPool> BleBatteryServer<'stack, 'server, 'conn, P> {
    pub(crate) fn new(server: &Server, conn: &'conn GattConnection<'stack, 'server, P>) -> Self {
        Self {
            battery_level: server.battery_service.level,
            battery_level_status: server.battery_service.level_status,
            conn,
        }
    }
}

impl<P: PacketPool> BleBatteryServer<'_, '_, '_, P> {
    pub(crate) async fn run(&mut self) {
        // Wait 2 seconds, ensure that gatt server has been started.
        Timer::after_secs(2).await;

        // Sentinel 73% on connect: macOS suppresses BAS readings of 0% so a
        // fresh GATT cache that has never been populated stays blank. By
        // pushing a non-zero distinguishable value immediately we coax the
        // menu into showing *something*; the heartbeat below overwrites it
        // with the real level as soon as BatteryProcessor has it.
        let mut last_level: u8 = 73;
        if let Some(BatteryState::Normal(level)) = BATTERY_UPDATE.try_take() {
            last_level = level.max(1);
        }
        if let Err(e) = self.battery_level.notify(self.conn, &last_level).await {
            error!("Failed to notify battery level (kobu initial): {:?}", e);
        }

        // Initial Battery Level Status push — same idea: get a real value into
        // the cached characteristic before macOS reads it.
        let mut last_charging = kobu_vbus_present();
        let status_bytes = kobu_encode_level_status(last_charging);
        if let Err(e) = self.battery_level_status.notify(self.conn, &status_bytes).await {
            error!("Failed to notify level status (kobu initial): {:?}", e);
        }

        loop {
            // Wake every 10 s (or sooner if BATTERY_UPDATE fires) so VBUS
            // plug/unplug shows up in the Bluetooth menu within ~10 s and the
            // host's cached characteristic value never drifts stale.
            let next = embassy_time::with_timeout(
                embassy_time::Duration::from_secs(10),
                BATTERY_UPDATE.wait(),
            )
            .await;
            if let Ok(BatteryState::Normal(level)) = next {
                last_level = level.max(1);
            }
            if let Err(e) = self.battery_level.notify(self.conn, &last_level).await {
                error!("Failed to notify battery level: {:?}", e);
            }

            let charging_now = kobu_vbus_present();
            last_charging = charging_now;
            let status_bytes = kobu_encode_level_status(last_charging);
            if let Err(e) = self.battery_level_status.notify(self.conn, &status_bytes).await {
                error!("Failed to notify level status: {:?}", e);
            }
        }
    }
}

/// True when the nRF52840's POWER peripheral reports VBUS present. Mirrors
/// `crate::status_led::vbus_present` in the kobu firmware so the BAS notify
/// loop can stay self-contained (no extra signal plumbing).
#[cfg(feature = "_nrf_ble")]
fn kobu_vbus_present() -> bool {
    embassy_nrf::pac::POWER.usbregstatus().read().vbusdetect()
}

#[cfg(not(feature = "_nrf_ble"))]
fn kobu_vbus_present() -> bool {
    false
}

/// Encode the BAS 1.1 Battery Level Status payload. See the doc comment on
/// `BatteryService::level_status` for the bit layout.
fn kobu_encode_level_status(charging: bool) -> [u8; 3] {
    // Battery is always present on kobu (bit 0 = 1).
    let mut power_state: u16 = 0b0000_0001;
    if charging {
        // bits 1..2 = 01 (wired external power present).
        power_state |= 0b0000_0010;
        // bits 5..6 = 01 (charging).
        power_state |= 0b0010_0000;
    } else {
        // bits 5..6 = 10 (discharging-active).
        power_state |= 0b0100_0000;
    }
    [0x00, (power_state & 0xff) as u8, ((power_state >> 8) & 0xff) as u8]
}

"##;

    let mut out = String::from(new_contents);
    out.push_str(MARKER);
    out.push('\n');

    fs::write(&path, out).unwrap_or_else(|e| {
        panic!("kobu: failed to write {}: {e}", path.display());
    });
}

/// Bump the acquisition time on every macro-generated SAADC channel from the
/// embassy-nrf default `Time::_10US` to `Time::_40US`. XIAO nRF52840 BLE's
/// on-module 1M / 1M BAT divider presents a ≈500 kΩ source impedance to
/// `P0_31`. With 10 µs the SAADC sample-and-hold capacitor never finishes
/// charging, so the ADC reads ≈0 and `BatteryProcessor` decodes 0%. nRF5
/// reference manual table for SAADC acquisition vs. source impedance maps
/// 500 kΩ → 40 µs, which is what we install here.
///
/// The patch targets the rmk-macro proc-macro crate's source (`adc.rs`) and
/// rewrites the quoted ChannelConfig construction so every battery /
/// joystick channel emitted by the macro picks up the new time. The change
/// is idempotent (marker line) and panics if the upstream fragment moves.
fn patch_rmk_macro_adc_acquisition_time() {
    const MARKER: &str = "// kobu: SAADC acquisition-time bump applied";
    const RMK_MACRO_VERSION: &str = "0.7.1";

    let Some(path) = find_rmk_macro_file(RMK_MACRO_VERSION, "src/input_device/adc.rs") else {
        println!(
            "cargo:warning=kobu: could not find rmk-macro-{RMK_MACRO_VERSION} adc.rs; \
             SAADC acquisition-time patch was not applied"
        );
        return;
    };

    println!("cargo:rerun-if-changed={}", path.display());

    let mut contents = fs::read_to_string(&path).unwrap_or_else(|e| {
        panic!("kobu: failed to read {}: {e}", path.display());
    });

    if contents.contains(MARKER) {
        return;
    }

    let replacements = [
        // Battery / generic single-ended channel.
        (
            "saadc::ChannelConfig::single_ended(p.#adc_pin_def.degrade_saadc())",
            "{ let mut __cfg = saadc::ChannelConfig::single_ended(p.#adc_pin_def.degrade_saadc()); __cfg.time = saadc::Time::_40US; __cfg }",
        ),
        // VDDH internal divider channel.
        (
            "saadc::ChannelConfig::single_ended(saadc::VddhDiv5Input.degrade_saadc())",
            "{ let mut __cfg = saadc::ChannelConfig::single_ended(saadc::VddhDiv5Input.degrade_saadc()); __cfg.time = saadc::Time::_40US; __cfg }",
        ),
    ];

    let mut applied = 0;
    for (from, to) in replacements {
        if contents.contains(from) {
            contents = contents.replace(from, to);
            applied += 1;
        }
    }

    if applied == 0 {
        panic!(
            "kobu: expected rmk-macro-{RMK_MACRO_VERSION} ChannelConfig::single_ended fragment missing in {}; \
             upstream may have changed — update firmware/build.rs",
            path.display()
        );
    }

    contents.push('\n');
    contents.push_str(MARKER);
    contents.push('\n');

    fs::write(&path, contents).unwrap_or_else(|e| {
        panic!("kobu: failed to write {}: {e}", path.display());
    });
}

fn find_rmk_macro_file(rmk_macro_version: &str, rel_path: &str) -> Option<PathBuf> {
    let home = env::var("HOME")
        .or_else(|_| env::var("USERPROFILE"))
        .ok()?;
    let src_root = PathBuf::from(home).join(".cargo/registry/src");
    let entries = fs::read_dir(&src_root).ok()?;
    let crate_dir = format!("rmk-macro-{rmk_macro_version}");
    let rel = Path::new(&crate_dir).join(rel_path);

    for entry in entries.flatten() {
        let candidate = entry.path().join(&rel);
        if candidate.is_file() {
            return Some(candidate);
        }
    }
    None
}

/// Drop the "only signal when the percent changes" guard inside
/// `BatteryProcessor::process` so `BATTERY_UPDATE.signal()` fires on every
/// `Event::Battery` the ADC produces.
///
/// Why: `BATTERY_UPDATE` is an embassy_sync `Signal`, single-consumer. The
/// kobu `BleBatteryServer::run` consumes it via `try_take` / `wait` on every
/// BLE connection. With the upstream guard, once a connection has drained
/// the Signal the BatteryProcessor stops refreshing it (because the
/// per-sample percent doesn't change), so the *next* connection's
/// `try_take` returns `None` and the kobu sentinel (100%) wins. With this
/// patch every ADC tick reposts the value, which lets reconnects see the
/// true level and lets the 60-second heartbeat loop in our patched
/// `BleBatteryServer` actually carry fresh data.
fn patch_rmk_battery_processor_signal() {
    const MARKER: &str = "// kobu: BatteryProcessor always-signal patch applied";
    const RMK_VERSION: &str = "0.8.2";

    let Some(path) = find_rmk_file(RMK_VERSION, "src/input_device/battery.rs") else {
        println!(
            "cargo:warning=kobu: could not find rmk-{RMK_VERSION} input_device/battery.rs; \
             BatteryProcessor always-signal patch was not applied"
        );
        return;
    };

    println!("cargo:rerun-if-changed={}", path.display());

    let mut contents = fs::read_to_string(&path).unwrap_or_else(|e| {
        panic!("kobu: failed to read {}: {e}", path.display());
    });

    if contents.contains(MARKER) {
        return;
    }

    let old_block = r#"                        // Update the battery state
                        if self.battery_state != BatteryState::Normal(battery_percent) {
                            self.battery_state = BatteryState::Normal(battery_percent);
                            // Send signal
                            BATTERY_UPDATE.signal(self.battery_state);
                        }"#;
    let new_block = r#"                        // kobu patch: always update state and re-signal so
                        // BleBatteryServer reconnects can always see the latest
                        // percent without needing the value to change first.
                        self.battery_state = BatteryState::Normal(battery_percent);
                        BATTERY_UPDATE.signal(self.battery_state);"#;

    if !contents.contains(old_block) {
        panic!(
            "kobu: expected rmk-{RMK_VERSION} BatteryProcessor signal block missing in {}; \
             upstream may have changed — update firmware/build.rs",
            path.display()
        );
    }
    contents = contents.replace(old_block, new_block);

    contents.push('\n');
    contents.push_str(MARKER);
    contents.push('\n');

    fs::write(&path, contents).unwrap_or_else(|e| {
        panic!("kobu: failed to write {}: {e}", path.display());
    });
}

/// Inject two `pub static AtomicU8` slots into rmk-0.8.2's `battery.rs` —
/// `KOBU_CENTRAL_BATTERY_PERCENT` and `KOBU_PERIPHERAL_BATTERY_PERCENT`.
/// The kobu firmware writes each side's decoded LiPo percentage into the
/// corresponding atomic from its bit-tag routing tap (see
/// `firmware/src/battery_source.rs`), and the patched `via/mod.rs`
/// `CustomGetValue` handler reads them back to answer Via Custom Channel
/// 0xC0 queries from `kobu-config`.
///
/// Atomics live inside rmk's crate because the `via/mod.rs` handler
/// (which we also patch) can only reach symbols visible from inside the
/// rmk crate. Marking them `pub` lets the kobu firmware crate write to
/// them via `rmk::input_device::battery::KOBU_*`.
fn patch_rmk_battery_kobu_atomics() {
    const MARKER: &str = "// kobu: battery atomics for via custom get applied";
    const RMK_VERSION: &str = "0.8.2";

    let Some(path) = find_rmk_file(RMK_VERSION, "src/input_device/battery.rs") else {
        println!(
            "cargo:warning=kobu: could not find rmk-{RMK_VERSION} input_device/battery.rs; \
             kobu atomics patch was not applied"
        );
        return;
    };

    println!("cargo:rerun-if-changed={}", path.display());

    let mut contents = fs::read_to_string(&path).unwrap_or_else(|e| {
        panic!("kobu: failed to read {}: {e}", path.display());
    });

    if contents.contains(MARKER) {
        return;
    }

    let anchor = "pub(crate) static BATTERY_UPDATE: Signal<crate::RawMutex, BatteryState> = Signal::new();";
    if !contents.contains(anchor) {
        panic!(
            "kobu: expected rmk-{RMK_VERSION} input_device/battery.rs anchor missing in {}; \
             upstream may have changed — update firmware/build.rs",
            path.display()
        );
    }
    let injected = "pub(crate) static BATTERY_UPDATE: Signal<crate::RawMutex, BatteryState> = Signal::new();\n\n// kobu: pub atomics for the Via Custom Get handler. Each side's LiPo\n// percentage (0..=100) is mirrored here from the kobu-side bit-tag tap\n// in firmware/src/battery_source.rs, so the patched via/mod.rs handler\n// can answer kobu-config's CustomGetValue(channel=0xC0, id=0x10/0x11)\n// queries without reaching across crates.\npub static KOBU_CENTRAL_BATTERY_PERCENT: core::sync::atomic::AtomicU8 = core::sync::atomic::AtomicU8::new(0);\npub static KOBU_PERIPHERAL_BATTERY_PERCENT: core::sync::atomic::AtomicU8 = core::sync::atomic::AtomicU8::new(0);";
    contents = contents.replace(anchor, injected);

    contents.push('\n');
    contents.push_str(MARKER);
    contents.push('\n');

    fs::write(&path, contents).unwrap_or_else(|e| {
        panic!("kobu: failed to write {}: {e}", path.display());
    });
}

/// Wire the RMK 0.8 `ViaCommand::CustomGetValue` stub up so the kobu-config
/// web UI's `Via Custom Channel 0xC0` queries return the current LiPo
/// percentage on each kobu half.
///
/// Upstream RMK leaves CustomGet/Set/Save as `warn!()`-only stubs (issue
/// #39 in kobu's tracker). We replace the get-side stub with a kobu-aware
/// branch: when channel == 0xC0, the handler reads the matching atomic
/// (id 0x10 = central, id 0x11 = peripheral) out of
/// `crate::input_device::battery::KOBU_*` and writes the percent into the
/// response buffer at index 3 (the standard Via custom-value reply layout).
///
/// Set / Save are left as warnings — kobu's battery values are read-only.
fn patch_rmk_via_custom_get_kobu() {
    // v3 marker covers the scroll-step divisor (id 0x08, 効き pass
    // 2026-08-16). Earlier kobu builds shipped v1 (battery-only) or v2
    // (settings table); all three cache states are detected and upgraded in
    // place so fresh and previously-patched rmk caches converge on the same
    // contents.
    const MARKER_V3: &str = "// kobu: via CustomGetValue handler for channel 0xC0 (v3 scroll-step) applied";
    const MARKER_V2: &str = "// kobu: via CustomGetValue handler for channel 0xC0 (v2 settings) applied";
    const MARKER_V1: &str = "// kobu: via CustomGetValue handler for channel 0xC0 applied";
    const RMK_VERSION: &str = "0.8.2";

    let Some(path) = find_rmk_file(RMK_VERSION, "src/host/via/mod.rs") else {
        println!(
            "cargo:warning=kobu: could not find rmk-{RMK_VERSION} host/via/mod.rs; \
             via CustomGet patch was not applied"
        );
        return;
    };

    println!("cargo:rerun-if-changed={}", path.display());

    let mut contents = fs::read_to_string(&path).unwrap_or_else(|e| {
        panic!("kobu: failed to read {}: {e}", path.display());
    });

    if contents.contains(MARKER_V3) {
        return;
    }

    // The block we're replacing depends on which kobu build (if any) already
    // patched this file. Cargo's registry cache survives across builds, so
    // the original `warn!()`-only stub, the v1 (battery-only) block, or the
    // v2 (settings-table) block may be present. Detect all three states.
    let original_block = r#"            ViaCommand::CustomGetValue => {
                // backlight/rgblight/rgb matrix/led matrix/audio settings here
                warn!("Custom get value -- not supported")
            }"#;
    let v1_block = r#"            ViaCommand::CustomGetValue => {
                // kobu Via Custom Channel 0xC0 — see firmware/src/config.rs and
                // web/src/protocol/customValue.ts for the id table. All kobu
                // ids are read-only from the host's perspective; the Set /
                // Save handlers still warn-and-drop.
                let channel = report.output_data[1];
                let id = report.output_data[2];
                if channel == 0xC0 {
                    match id {
                        0x10 => {
                            report.input_data[3] = crate::input_device::battery::KOBU_CENTRAL_BATTERY_PERCENT
                                .load(core::sync::atomic::Ordering::Relaxed);
                        }
                        0x11 => {
                            report.input_data[3] = crate::input_device::battery::KOBU_PERIPHERAL_BATTERY_PERCENT
                                .load(core::sync::atomic::Ordering::Relaxed);
                        }
                        _ => {
                            warn!("kobu: unknown CustomGetValue id 0x{:02X} on channel 0xC0", id);
                        }
                    }
                } else {
                    warn!("Custom get value -- not supported");
                }
            }"#;

    let v2_block = r#"            ViaCommand::CustomGetValue => {
                // kobu Via Custom Channel 0xC0 — see firmware/src/config.rs and
                // web/src/protocol/customValue.ts for the id table.
                // - 0x01..0x07: read/write runtime settings backed by atomics
                //   in crate::input_device::battery (KOBU_*); the Set arm
                //   updates the same atomics so reads see live state.
                // - 0x10/0x11:  read-only battery percentages mirrored from
                //   kobu's source tap.
                let channel = report.output_data[1];
                let id = report.output_data[2];
                if channel == 0xC0 {
                    use core::sync::atomic::Ordering;
                    let kc = &crate::input_device::battery::KOBU_CENTRAL_BATTERY_PERCENT;
                    let kp = &crate::input_device::battery::KOBU_PERIPHERAL_BATTERY_PERCENT;
                    match id {
                        0x01 => {
                            // u16 BE at bytes 3..5
                            let v = crate::input_device::battery::KOBU_TRACKBALL_CPI.load(Ordering::Relaxed);
                            report.input_data[3] = (v >> 8) as u8;
                            report.input_data[4] = (v & 0xFF) as u8;
                        }
                        0x02 => {
                            report.input_data[3] = crate::input_device::battery::KOBU_SCROLL_THROTTLE_MS.load(Ordering::Relaxed);
                        }
                        0x03 => {
                            report.input_data[3] = if crate::input_device::battery::KOBU_SCROLL_INVERT_X.load(Ordering::Relaxed) { 1 } else { 0 };
                        }
                        0x04 => {
                            report.input_data[3] = if crate::input_device::battery::KOBU_SCROLL_INVERT_Y.load(Ordering::Relaxed) { 1 } else { 0 };
                        }
                        0x05 => {
                            let v = crate::input_device::battery::KOBU_STATUS_LED_PURPLE_HOLD_MS.load(Ordering::Relaxed);
                            report.input_data[3] = (v >> 8) as u8;
                            report.input_data[4] = (v & 0xFF) as u8;
                        }
                        0x06 => {
                            report.input_data[3] = crate::input_device::battery::KOBU_STATUS_LED_BAT_HIGH.load(Ordering::Relaxed);
                        }
                        0x07 => {
                            report.input_data[3] = crate::input_device::battery::KOBU_STATUS_LED_BAT_LOW.load(Ordering::Relaxed);
                        }
                        0x10 => {
                            report.input_data[3] = kc.load(Ordering::Relaxed);
                        }
                        0x11 => {
                            report.input_data[3] = kp.load(Ordering::Relaxed);
                        }
                        _ => {
                            warn!("kobu: unknown CustomGetValue id 0x{:02X} on channel 0xC0", id);
                        }
                    }
                } else {
                    warn!("Custom get value -- not supported");
                }
            }"#;

    let v3_block = r#"            ViaCommand::CustomGetValue => {
                // kobu Via Custom Channel 0xC0 — see firmware/src/config.rs and
                // web/src/protocol/customValue.ts for the id table.
                // - 0x01..0x08: read/write runtime settings backed by atomics
                //   in crate::input_device::battery (KOBU_*); the Set arm
                //   updates the same atomics so reads see live state.
                // - 0x10/0x11:  read-only battery percentages mirrored from
                //   kobu's source tap.
                let channel = report.output_data[1];
                let id = report.output_data[2];
                if channel == 0xC0 {
                    use core::sync::atomic::Ordering;
                    let kc = &crate::input_device::battery::KOBU_CENTRAL_BATTERY_PERCENT;
                    let kp = &crate::input_device::battery::KOBU_PERIPHERAL_BATTERY_PERCENT;
                    match id {
                        0x01 => {
                            // u16 BE at bytes 3..5
                            let v = crate::input_device::battery::KOBU_TRACKBALL_CPI.load(Ordering::Relaxed);
                            report.input_data[3] = (v >> 8) as u8;
                            report.input_data[4] = (v & 0xFF) as u8;
                        }
                        0x02 => {
                            report.input_data[3] = crate::input_device::battery::KOBU_SCROLL_THROTTLE_MS.load(Ordering::Relaxed);
                        }
                        0x03 => {
                            report.input_data[3] = if crate::input_device::battery::KOBU_SCROLL_INVERT_X.load(Ordering::Relaxed) { 1 } else { 0 };
                        }
                        0x04 => {
                            report.input_data[3] = if crate::input_device::battery::KOBU_SCROLL_INVERT_Y.load(Ordering::Relaxed) { 1 } else { 0 };
                        }
                        0x05 => {
                            let v = crate::input_device::battery::KOBU_STATUS_LED_PURPLE_HOLD_MS.load(Ordering::Relaxed);
                            report.input_data[3] = (v >> 8) as u8;
                            report.input_data[4] = (v & 0xFF) as u8;
                        }
                        0x06 => {
                            report.input_data[3] = crate::input_device::battery::KOBU_STATUS_LED_BAT_HIGH.load(Ordering::Relaxed);
                        }
                        0x07 => {
                            report.input_data[3] = crate::input_device::battery::KOBU_STATUS_LED_BAT_LOW.load(Ordering::Relaxed);
                        }
                        0x08 => {
                            report.input_data[3] = crate::input_device::battery::KOBU_SCROLL_STEP.load(Ordering::Relaxed);
                        }
                        0x10 => {
                            report.input_data[3] = kc.load(Ordering::Relaxed);
                        }
                        0x11 => {
                            report.input_data[3] = kp.load(Ordering::Relaxed);
                        }
                        _ => {
                            warn!("kobu: unknown CustomGetValue id 0x{:02X} on channel 0xC0", id);
                        }
                    }
                } else {
                    warn!("Custom get value -- not supported");
                }
            }"#;

    let target = if contents.contains(v2_block) {
        v2_block
    } else if contents.contains(v1_block) {
        v1_block
    } else if contents.contains(original_block) {
        original_block
    } else {
        panic!(
            "kobu: expected rmk-{RMK_VERSION} host/via/mod.rs CustomGetValue block missing in {} (no original / kobu-v1 / kobu-v2 shape found); \
             upstream may have changed — update firmware/build.rs",
            path.display()
        );
    };
    contents = contents.replace(target, v3_block);

    // Strip stale v1/v2 markers, append v3.
    if contents.contains(MARKER_V1) {
        contents = contents.replace(&format!("\n{}\n", MARKER_V1), "\n");
    }
    if contents.contains(MARKER_V2) {
        contents = contents.replace(&format!("\n{}\n", MARKER_V2), "\n");
    }
    contents.push('\n');
    contents.push_str(MARKER_V3);
    contents.push('\n');

    fs::write(&path, contents).unwrap_or_else(|e| {
        panic!("kobu: failed to write {}: {e}", path.display());
    });
}

/// Extend the `ViaCommand::CustomSetValue` arm so writes for kobu
/// channel `0xC0`, ids `0x01..=0x08` mutate the runtime config atomics
/// in `crate::input_device::battery::KOBU_*`. The existing
/// peripheral-bootloader-jump branch (channel 0xC0 / id 0x12) is
/// preserved verbatim; only the trailing `else` warn branch is replaced.
fn patch_rmk_via_custom_set_kobu_settings() {
    // v2 marker covers the scroll-step divisor (id 0x08, 効き pass
    // 2026-08-16). A registry cache previously patched by an older build
    // carries the v1 marker + settings block; both cache states are
    // detected and upgraded in place.
    const MARKER_V2: &str = "// kobu: via CustomSetValue handler for channel 0xC0 (v2 scroll-step) applied";
    const MARKER_V1: &str = "// kobu: via CustomSetValue handler for channel 0xC0 settings applied";
    const RMK_VERSION: &str = "0.8.2";

    let Some(path) = find_rmk_file(RMK_VERSION, "src/host/via/mod.rs") else {
        return;
    };

    println!("cargo:rerun-if-changed={}", path.display());

    let mut contents = fs::read_to_string(&path).unwrap_or_else(|e| {
        panic!("kobu: failed to read {}: {e}", path.display());
    });

    if contents.contains(MARKER_V2) {
        return;
    }

    // Anchor reflects the bootloader-jump-patched Set arm (see
    // `patch_rmk_peripheral_bootloader_jump`). That patch always runs
    // before this one so on a FRESH cache the anchor below is what's in
    // the file at build time; a previously-patched cache instead carries
    // the v1 settings block.
    let bootloader_patched_block = r#"            ViaCommand::CustomSetValue => {
                // kobu Via Custom Channel 0xC0 — write-only kobu commands
                // (currently just 0x12 = peripheral bootloader jump).
                let channel = report.output_data[1];
                let id = report.output_data[2];
                let value = report.output_data[3];
                #[cfg(all(feature = "_ble", feature = "split", feature = "controller"))]
                if channel == 0xC0 && id == 0x12 && value == 1 {
                    warn!("kobu: publishing PeripheralBootloaderJump from Via CustomSetValue");
                    crate::channel::send_controller_event_new(crate::event::ControllerEvent::PeripheralBootloaderJump);
                } else {
                    warn!("Custom set value -- not supported (channel={:02X} id={:02X})", channel, id);
                }
                #[cfg(not(all(feature = "_ble", feature = "split", feature = "controller")))]
                warn!("Custom set value -- not supported (channel={:02X} id={:02X})", channel, id);
            }"#;

    let v1_settings_block = r#"            ViaCommand::CustomSetValue => {
                // kobu Via Custom Channel 0xC0.
                //   0x01..=0x07: runtime settings — write into the matching
                //                atomic in crate::input_device::battery.
                //                Clamping mirrors firmware/src/config.rs.
                //   0x12:        peripheral bootloader-jump relay (BLE).
                let channel = report.output_data[1];
                let id = report.output_data[2];
                let value = report.output_data[3];
                let value2 = report.output_data[4];
                if channel == 0xC0 {
                    use core::sync::atomic::Ordering;
                    match id {
                        0x01 => {
                            // u16 BE, clamp 200..=3200 — matches
                            // firmware/src/config.rs::apply.
                            let raw = ((value as u16) << 8) | (value2 as u16);
                            let clamped = if raw < 200 { 200 } else if raw > 3200 { 3200 } else { raw };
                            crate::input_device::battery::KOBU_TRACKBALL_CPI.store(clamped, Ordering::Relaxed);
                        }
                        0x02 => {
                            let v = if value > 50 { 50 } else { value };
                            crate::input_device::battery::KOBU_SCROLL_THROTTLE_MS.store(v, Ordering::Relaxed);
                        }
                        0x03 => {
                            crate::input_device::battery::KOBU_SCROLL_INVERT_X.store(value != 0, Ordering::Relaxed);
                        }
                        0x04 => {
                            crate::input_device::battery::KOBU_SCROLL_INVERT_Y.store(value != 0, Ordering::Relaxed);
                        }
                        0x05 => {
                            // u16 BE, clamp 0..=2000.
                            let raw = ((value as u16) << 8) | (value2 as u16);
                            let clamped = if raw > 2000 { 2000 } else { raw };
                            crate::input_device::battery::KOBU_STATUS_LED_PURPLE_HOLD_MS.store(clamped, Ordering::Relaxed);
                        }
                        0x06 => {
                            // High threshold ≥ 20, ≤ 100. Keep low<high invariant.
                            let mut high = if value < 20 { 20 } else if value > 100 { 100 } else { value };
                            let mut low = crate::input_device::battery::KOBU_STATUS_LED_BAT_LOW.load(Ordering::Relaxed);
                            if low >= high { core::mem::swap(&mut low, &mut high); }
                            crate::input_device::battery::KOBU_STATUS_LED_BAT_HIGH.store(high, Ordering::Relaxed);
                            crate::input_device::battery::KOBU_STATUS_LED_BAT_LOW.store(low, Ordering::Relaxed);
                        }
                        0x07 => {
                            let mut low = if value > 50 { 50 } else { value };
                            let mut high = crate::input_device::battery::KOBU_STATUS_LED_BAT_HIGH.load(Ordering::Relaxed);
                            if low >= high { core::mem::swap(&mut low, &mut high); }
                            crate::input_device::battery::KOBU_STATUS_LED_BAT_HIGH.store(high, Ordering::Relaxed);
                            crate::input_device::battery::KOBU_STATUS_LED_BAT_LOW.store(low, Ordering::Relaxed);
                        }
                        #[cfg(all(feature = "_ble", feature = "split", feature = "controller"))]
                        0x12 if value == 1 => {
                            warn!("kobu: publishing PeripheralBootloaderJump from Via CustomSetValue");
                            crate::channel::send_controller_event_new(crate::event::ControllerEvent::PeripheralBootloaderJump);
                        }
                        _ => {
                            warn!("kobu: unknown CustomSetValue id 0x{:02X} on channel 0xC0", id);
                        }
                    }
                } else {
                    warn!("Custom set value -- not supported (channel={:02X} id={:02X})", channel, id);
                }
            }"#;

    let v2_settings_block = r#"            ViaCommand::CustomSetValue => {
                // kobu Via Custom Channel 0xC0.
                //   0x01..=0x08: runtime settings — write into the matching
                //                atomic in crate::input_device::battery.
                //                Clamping mirrors firmware/src/config.rs.
                //   0x12:        peripheral bootloader-jump relay (BLE).
                let channel = report.output_data[1];
                let id = report.output_data[2];
                let value = report.output_data[3];
                let value2 = report.output_data[4];
                if channel == 0xC0 {
                    use core::sync::atomic::Ordering;
                    match id {
                        0x01 => {
                            // u16 BE, clamp 200..=3200 — matches
                            // firmware/src/config.rs::apply.
                            let raw = ((value as u16) << 8) | (value2 as u16);
                            let clamped = if raw < 200 { 200 } else if raw > 3200 { 3200 } else { raw };
                            crate::input_device::battery::KOBU_TRACKBALL_CPI.store(clamped, Ordering::Relaxed);
                        }
                        0x02 => {
                            let v = if value > 50 { 50 } else { value };
                            crate::input_device::battery::KOBU_SCROLL_THROTTLE_MS.store(v, Ordering::Relaxed);
                        }
                        0x03 => {
                            crate::input_device::battery::KOBU_SCROLL_INVERT_X.store(value != 0, Ordering::Relaxed);
                        }
                        0x04 => {
                            crate::input_device::battery::KOBU_SCROLL_INVERT_Y.store(value != 0, Ordering::Relaxed);
                        }
                        0x05 => {
                            // u16 BE, clamp 0..=2000.
                            let raw = ((value as u16) << 8) | (value2 as u16);
                            let clamped = if raw > 2000 { 2000 } else { raw };
                            crate::input_device::battery::KOBU_STATUS_LED_PURPLE_HOLD_MS.store(clamped, Ordering::Relaxed);
                        }
                        0x06 => {
                            // High threshold ≥ 20, ≤ 100. Keep low<high invariant.
                            let mut high = if value < 20 { 20 } else if value > 100 { 100 } else { value };
                            let mut low = crate::input_device::battery::KOBU_STATUS_LED_BAT_LOW.load(Ordering::Relaxed);
                            if low >= high { core::mem::swap(&mut low, &mut high); }
                            crate::input_device::battery::KOBU_STATUS_LED_BAT_HIGH.store(high, Ordering::Relaxed);
                            crate::input_device::battery::KOBU_STATUS_LED_BAT_LOW.store(low, Ordering::Relaxed);
                        }
                        0x07 => {
                            let mut low = if value > 50 { 50 } else { value };
                            let mut high = crate::input_device::battery::KOBU_STATUS_LED_BAT_HIGH.load(Ordering::Relaxed);
                            if low >= high { core::mem::swap(&mut low, &mut high); }
                            crate::input_device::battery::KOBU_STATUS_LED_BAT_HIGH.store(high, Ordering::Relaxed);
                            crate::input_device::battery::KOBU_STATUS_LED_BAT_LOW.store(low, Ordering::Relaxed);
                        }
                        0x08 => {
                            // Scroll divisor (raw counts per wheel tick),
                            // clamp 4..=120 — matches firmware/src/config.rs.
                            let v = if value < 4 { 4 } else if value > 120 { 120 } else { value };
                            crate::input_device::battery::KOBU_SCROLL_STEP.store(v, Ordering::Relaxed);
                        }
                        #[cfg(all(feature = "_ble", feature = "split", feature = "controller"))]
                        0x12 if value == 1 => {
                            warn!("kobu: publishing PeripheralBootloaderJump from Via CustomSetValue");
                            crate::channel::send_controller_event_new(crate::event::ControllerEvent::PeripheralBootloaderJump);
                        }
                        _ => {
                            warn!("kobu: unknown CustomSetValue id 0x{:02X} on channel 0xC0", id);
                        }
                    }
                } else {
                    warn!("Custom set value -- not supported (channel={:02X} id={:02X})", channel, id);
                }
            }"#;

    let target = if contents.contains(v1_settings_block) {
        v1_settings_block
    } else if contents.contains(bootloader_patched_block) {
        bootloader_patched_block
    } else {
        panic!(
            "kobu: expected rmk-{RMK_VERSION} host/via/mod.rs CustomSetValue block missing in {} (neither bootloader-patched nor kobu-v1-settings shape found); \
             upstream may have changed or peripheral-bootloader-jump patch is out of sync — update firmware/build.rs",
            path.display()
        );
    };
    contents = contents.replace(target, v2_settings_block);

    // Strip the stale v1 marker, append v2.
    if contents.contains(MARKER_V1) {
        contents = contents.replace(&format!("\n{}\n", MARKER_V1), "\n");
    }
    contents.push('\n');
    contents.push_str(MARKER_V2);
    contents.push('\n');

    fs::write(&path, contents).unwrap_or_else(|e| {
        panic!("kobu: failed to write {}: {e}", path.display());
    });
}

/// Patch `ViaCommand::CustomSave` so saves on kobu channel `0xC0` are a
/// silent no-op success. Writes to the kobu atomics are applied
/// immediately by the Set handler — RMK 0.8 has no persistence layer
/// for our channel, so Save is purely a vial-gui-compat ack.
fn patch_rmk_via_custom_save_kobu() {
    const MARKER: &str = "// kobu: via CustomSave handler for channel 0xC0 applied";
    const RMK_VERSION: &str = "0.8.2";

    let Some(path) = find_rmk_file(RMK_VERSION, "src/host/via/mod.rs") else {
        return;
    };

    println!("cargo:rerun-if-changed={}", path.display());

    let mut contents = fs::read_to_string(&path).unwrap_or_else(|e| {
        panic!("kobu: failed to read {}: {e}", path.display());
    });

    if contents.contains(MARKER) {
        return;
    }

    let old_block = r#"            ViaCommand::CustomSave => {
                // backlight/rgblight/rgb matrix/led matrix/audio settings here
                warn!("Custom get value -- not supported")
            }"#;
    let new_block = r#"            ViaCommand::CustomSave => {
                // kobu Via Custom Channel 0xC0 — silently ack. Atomics
                // are mutated synchronously by CustomSetValue; vial-gui
                // -style tooling expects an explicit Save step, so we
                // succeed without doing anything for our channel.
                let channel = report.output_data[1];
                if channel != 0xC0 {
                    warn!("Custom save -- not supported (channel={:02X})", channel);
                }
            }"#;

    if !contents.contains(old_block) {
        panic!(
            "kobu: expected rmk-{RMK_VERSION} host/via/mod.rs CustomSave block missing in {}; \
             upstream may have changed — update firmware/build.rs",
            path.display()
        );
    }
    contents = contents.replace(old_block, new_block);

    contents.push('\n');
    contents.push_str(MARKER);
    contents.push('\n');

    fs::write(&path, contents).unwrap_or_else(|e| {
        panic!("kobu: failed to write {}: {e}", path.display());
    });
}

/// Add `pub static` atomics for kobu's writable runtime settings into
/// `rmk::input_device::battery`. Co-located with the existing battery
/// atomics so the Via Custom Get/Set handlers can reach them via a
/// single import path. Mirrors the schema in
/// `firmware/src/config.rs::KobuSettings`.
fn patch_rmk_kobu_settings_atomics() {
    // v2 marker covers the scroll-step divisor added by the 効き pass
    // (2026-08-16). A registry cache previously patched by an older build
    // carries the v1 marker + every static except KOBU_SCROLL_STEP; we top
    // the file up incrementally so fresh and previously-patched caches
    // converge on the same contents.
    const MARKER_V2: &str = "// kobu: writable runtime settings atomics (v2 scroll-step) applied";
    const MARKER_V1: &str = "// kobu: writable runtime settings atomics applied";
    const RMK_VERSION: &str = "0.8.2";

    let Some(path) = find_rmk_file(RMK_VERSION, "src/input_device/battery.rs") else {
        return;
    };

    println!("cargo:rerun-if-changed={}", path.display());

    let mut contents = fs::read_to_string(&path).unwrap_or_else(|e| {
        panic!("kobu: failed to read {}: {e}", path.display());
    });

    if contents.contains(MARKER_V2) {
        return;
    }

    // Keep in sync with `KobuSettings::default().scroll_step` and the Set
    // handler clamp in `patch_rmk_via_custom_set_kobu_settings`.
    const SCROLL_STEP_STATIC: &str = "pub static KOBU_SCROLL_STEP: core::sync::atomic::AtomicU8 = core::sync::atomic::AtomicU8::new(30);";

    if contents.contains(MARKER_V1) {
        // v1-patched cache: append the new static after the last v1 one.
        let anchor = "pub static KOBU_STATUS_LED_BAT_LOW: core::sync::atomic::AtomicU8 = core::sync::atomic::AtomicU8::new(20);";
        if !contents.contains(anchor) {
            panic!(
                "kobu: v1 settings-atomics marker present but KOBU_STATUS_LED_BAT_LOW anchor missing in {}; \
                 registry cache is in an unexpected state — delete the rmk-{RMK_VERSION} registry src dir and rebuild",
                path.display()
            );
        }
        contents = contents.replace(anchor, &format!("{anchor}\n{SCROLL_STEP_STATIC}"));
        contents = contents.replace(&format!("\n{MARKER_V1}\n"), "\n");
    } else {
        // Fresh cache: inject the whole settings block. Anchor: the last
        // line of the battery-percent injection from
        // `patch_rmk_battery_kobu_atomics`. That patch runs before this
        // one, so the anchor is always in the file at this point.
        let anchor = "pub static KOBU_PERIPHERAL_BATTERY_PERCENT: core::sync::atomic::AtomicU8 = core::sync::atomic::AtomicU8::new(0);";
        if !contents.contains(anchor) {
            panic!(
                "kobu: expected battery-percent anchor in rmk-{RMK_VERSION} input_device/battery.rs at {}; \
                 patch_rmk_battery_kobu_atomics must run first — order in build.rs::main",
                path.display()
            );
        }
        let injected = format!(
            "{anchor}\n\n// kobu: writable runtime settings. Mirrors firmware/src/config.rs schema.\n// The Via Custom Set handler in host/via/mod.rs writes here on a host\n// SetValue; firmware/src/{{trackball,status_led}}.rs read via thin\n// helpers in firmware/src/config.rs. Default values must match\n// `KobuSettings::default()` so a fresh build behaves identically.\npub static KOBU_TRACKBALL_CPI: core::sync::atomic::AtomicU16 = core::sync::atomic::AtomicU16::new(1000);\npub static KOBU_SCROLL_THROTTLE_MS: core::sync::atomic::AtomicU8 = core::sync::atomic::AtomicU8::new(0);\npub static KOBU_SCROLL_INVERT_X: core::sync::atomic::AtomicBool = core::sync::atomic::AtomicBool::new(false);\npub static KOBU_SCROLL_INVERT_Y: core::sync::atomic::AtomicBool = core::sync::atomic::AtomicBool::new(false);\npub static KOBU_STATUS_LED_PURPLE_HOLD_MS: core::sync::atomic::AtomicU16 = core::sync::atomic::AtomicU16::new(200);\npub static KOBU_STATUS_LED_BAT_HIGH: core::sync::atomic::AtomicU8 = core::sync::atomic::AtomicU8::new(60);\npub static KOBU_STATUS_LED_BAT_LOW: core::sync::atomic::AtomicU8 = core::sync::atomic::AtomicU8::new(20);\n{SCROLL_STEP_STATIC}"
        );
        contents = contents.replace(anchor, &injected);
    }

    contents.push('\n');
    contents.push_str(MARKER_V2);
    contents.push('\n');

    fs::write(&path, contents).unwrap_or_else(|e| {
        panic!("kobu: failed to write {}: {e}", path.display());
    });
}

/// Wire a split-link bootloader-jump relay so kobu-config can flash the
/// peripheral without the user double-tapping its physical RESET button.
/// Path: web UI → Vial `CustomSetValue(channel=0xC0, id=0x12, value=1)` →
/// central publishes `ControllerEvent::PeripheralBootloaderJump` →
/// `PeripheralManager::run` writes `SplitMessage::PeripheralBootloaderJump`
/// to the peripheral over the BLE split link → peripheral's
/// `SplitPeripheral::run` calls `crate::boot::jump_to_bootloader()` and
/// the device reboots into UF2 mode.
///
/// This is the deferred "split-bootloader-relay" follow-up tracked in
/// kobu's memory (`project-kobu-rmk`). It touches five upstream rmk
/// files; each `replacements` entry has its own panic-on-drift sentinel.
fn patch_rmk_peripheral_bootloader_jump() {
    const MARKER: &str = "// kobu: peripheral bootloader jump relay applied";
    const RMK_VERSION: &str = "0.8.2";

    let mut applied_any = false;

    // ── event.rs: add ControllerEvent::PeripheralBootloaderJump ───────
    if let Some(path) = find_rmk_file(RMK_VERSION, "src/event.rs") {
        let contents = fs::read_to_string(&path).unwrap_or_else(|e| {
            panic!("kobu: failed to read {}: {e}", path.display());
        });
        if !contents.contains(MARKER) {
            println!("cargo:rerun-if-changed={}", path.display());
            let from = "    #[cfg(all(feature = \"_ble\", feature = \"split\"))]\n    ClearPeer,";
            let to = "    #[cfg(all(feature = \"_ble\", feature = \"split\"))]\n    ClearPeer,\n    /// kobu: trigger peripheral to reboot into UF2 bootloader, central → peripheral via split link\n    #[cfg(all(feature = \"_ble\", feature = \"split\"))]\n    PeripheralBootloaderJump,";
            if !contents.contains(from) {
                panic!(
                    "kobu: expected rmk-{RMK_VERSION} event.rs ClearPeer anchor missing in {}; \
                     upstream may have changed — update firmware/build.rs",
                    path.display()
                );
            }
            let mut new_contents = contents.replace(from, to);
            new_contents.push('\n');
            new_contents.push_str(MARKER);
            new_contents.push('\n');
            fs::write(&path, new_contents).unwrap_or_else(|e| {
                panic!("kobu: failed to write {}: {e}", path.display());
            });
            applied_any = true;
        }
    }

    // ── split/mod.rs: add SplitMessage::PeripheralBootloaderJump ──────
    if let Some(path) = find_rmk_file(RMK_VERSION, "src/split/mod.rs") {
        let contents = fs::read_to_string(&path).unwrap_or_else(|e| {
            panic!("kobu: failed to read {}: {e}", path.display());
        });
        if !contents.contains(MARKER) {
            println!("cargo:rerun-if-changed={}", path.display());
            let from = "    /// Layer number from central to peripheral\n    Layer(u8),\n}";
            let to = "    /// Layer number from central to peripheral\n    Layer(u8),\n    /// kobu: tell peripheral to reboot into UF2 bootloader (central → peripheral)\n    PeripheralBootloaderJump,\n}";
            if !contents.contains(from) {
                panic!(
                    "kobu: expected rmk-{RMK_VERSION} split/mod.rs Layer anchor missing in {}; \
                     upstream may have changed — update firmware/build.rs",
                    path.display()
                );
            }
            let mut new_contents = contents.replace(from, to);
            new_contents.push('\n');
            new_contents.push_str(MARKER);
            new_contents.push('\n');
            fs::write(&path, new_contents).unwrap_or_else(|e| {
                panic!("kobu: failed to write {}: {e}", path.display());
            });
            applied_any = true;
        }
    }

    // ── split/driver.rs: PeripheralManager handles the controller event ─
    if let Some(path) = find_rmk_file(RMK_VERSION, "src/split/driver.rs") {
        let contents = fs::read_to_string(&path).unwrap_or_else(|e| {
            panic!("kobu: failed to read {}: {e}", path.display());
        });
        if !contents.contains(MARKER) {
            println!("cargo:rerun-if-changed={}", path.display());
            let from = "                        ControllerEvent::Layer(layer) => {";
            let to = "                        #[cfg(all(feature = \"_ble\", feature = \"split\"))]\n                        ControllerEvent::PeripheralBootloaderJump => {\n                            debug!(\"kobu: relaying PeripheralBootloaderJump to peripheral {}\", self.id);\n                            if let Err(e) = self.transceiver.write(&SplitMessage::PeripheralBootloaderJump).await {\n                                match e {\n                                    SplitDriverError::Disconnected => return,\n                                    _ => error!(\"SplitDriver write error: {:?}\", e),\n                                }\n                            }\n                        }\n                        ControllerEvent::Layer(layer) => {";
            if !contents.contains(from) {
                panic!(
                    "kobu: expected rmk-{RMK_VERSION} split/driver.rs ControllerEvent::Layer anchor missing in {}; \
                     upstream may have changed — update firmware/build.rs",
                    path.display()
                );
            }
            let mut new_contents = contents.replace(from, to);
            new_contents.push('\n');
            new_contents.push_str(MARKER);
            new_contents.push('\n');
            fs::write(&path, new_contents).unwrap_or_else(|e| {
                panic!("kobu: failed to write {}: {e}", path.display());
            });
            applied_any = true;
        }
    }

    // ── split/peripheral.rs: peripheral side handles the split message ─
    if let Some(path) = find_rmk_file(RMK_VERSION, "src/split/peripheral.rs") {
        let contents = fs::read_to_string(&path).unwrap_or_else(|e| {
            panic!("kobu: failed to read {}: {e}", path.display());
        });
        if !contents.contains(MARKER) {
            println!("cargo:rerun-if-changed={}", path.display());
            let from = "                        SplitMessage::Layer(layer) => {";
            let to = "                        SplitMessage::PeripheralBootloaderJump => {\n                            info!(\"kobu: received bootloader-jump from central, rebooting into UF2 mode\");\n                            crate::boot::jump_to_bootloader();\n                        }\n                        SplitMessage::Layer(layer) => {";
            if !contents.contains(from) {
                panic!(
                    "kobu: expected rmk-{RMK_VERSION} split/peripheral.rs SplitMessage::Layer anchor missing in {}; \
                     upstream may have changed — update firmware/build.rs",
                    path.display()
                );
            }
            let mut new_contents = contents.replace(from, to);
            new_contents.push('\n');
            new_contents.push_str(MARKER);
            new_contents.push('\n');
            fs::write(&path, new_contents).unwrap_or_else(|e| {
                panic!("kobu: failed to write {}: {e}", path.display());
            });
            applied_any = true;
        }
    }

    // ── via/mod.rs: CustomSetValue handler for channel 0xC0 id 0x12 ───
    if let Some(path) = find_rmk_file(RMK_VERSION, "src/host/via/mod.rs") {
        let contents = fs::read_to_string(&path).unwrap_or_else(|e| {
            panic!("kobu: failed to read {}: {e}", path.display());
        });
        if !contents.contains(MARKER) {
            println!("cargo:rerun-if-changed={}", path.display());
            let from = "            ViaCommand::CustomSetValue => {\n                // backlight/rgblight/rgb matrix/led matrix/audio settings here\n                warn!(\"Custom set value -- not supported\")\n            }";
            let to = "            ViaCommand::CustomSetValue => {\n                // kobu Via Custom Channel 0xC0 — write-only kobu commands\n                // (currently just 0x12 = peripheral bootloader jump).\n                let channel = report.output_data[1];\n                let id = report.output_data[2];\n                let value = report.output_data[3];\n                #[cfg(all(feature = \"_ble\", feature = \"split\", feature = \"controller\"))]\n                if channel == 0xC0 && id == 0x12 && value == 1 {\n                    warn!(\"kobu: publishing PeripheralBootloaderJump from Via CustomSetValue\");\n                    crate::channel::send_controller_event_new(crate::event::ControllerEvent::PeripheralBootloaderJump);\n                } else {\n                    warn!(\"Custom set value -- not supported (channel={:02X} id={:02X})\", channel, id);\n                }\n                #[cfg(not(all(feature = \"_ble\", feature = \"split\", feature = \"controller\")))]\n                warn!(\"Custom set value -- not supported (channel={:02X} id={:02X})\", channel, id);\n            }";
            if !contents.contains(from) {
                panic!(
                    "kobu: expected rmk-{RMK_VERSION} host/via/mod.rs CustomSetValue stub missing in {}; \
                     upstream may have changed — update firmware/build.rs",
                    path.display()
                );
            }
            let mut new_contents = contents.replace(from, to);
            new_contents.push('\n');
            new_contents.push_str(MARKER);
            new_contents.push('\n');
            fs::write(&path, new_contents).unwrap_or_else(|e| {
                panic!("kobu: failed to write {}: {e}", path.display());
            });
            applied_any = true;
        }
    }

    if !applied_any {
        println!(
            "cargo:warning=kobu: peripheral bootloader jump relay patch — no files modified (already applied or rmk-{RMK_VERSION} not found)"
        );
    }
}

/// Speed up macOS Bluetooth discovery + (re)pairing by lowering the host-
/// facing advertising interval from RMK's 200 ms default to 30 ms.
///
/// At 200 ms the device advertises only 5×/s; macOS scan windows often
/// took 10+ s to surface kobu in the Bluetooth picker. Apple's Accessory
/// Design Guidelines recommend 20–152.5 ms for connectable peripherals,
/// and 30 ms is the standard "fast pair" sweet spot — small enough for
/// near-instant discovery, large enough that battery cost is negligible
/// (and advertising stops once a host connects anyway).
fn patch_rmk_host_advertise_fast() {
    const MARKER: &str = "// kobu: host advertise interval lowered to 30 ms applied";
    const RMK_VERSION: &str = "0.8.2";

    let Some(path) = find_rmk_file(RMK_VERSION, "src/ble/mod.rs") else {
        return;
    };

    println!("cargo:rerun-if-changed={}", path.display());

    let mut contents = fs::read_to_string(&path).unwrap_or_else(|e| {
        panic!("kobu: failed to read {}: {e}", path.display());
    });

    if contents.contains(MARKER) {
        return;
    }

    // The Le1M lines are themselves a kobu patch (`patch_rmk_ble_for_macos`),
    // which runs before this one — so this anchor matches the post-patched
    // state of the file on every build.
    let old_block = r#"    let advertise_config = AdvertisementParameters {
        primary_phy: PhyKind::Le1M,
        secondary_phy: PhyKind::Le1M,
        tx_power: TxPower::Plus8dBm,
        interval_min: Duration::from_millis(200),
        interval_max: Duration::from_millis(200),
        ..Default::default()
    };"#;
    let new_block = r#"    let advertise_config = AdvertisementParameters {
        primary_phy: PhyKind::Le1M,
        secondary_phy: PhyKind::Le1M,
        tx_power: TxPower::Plus8dBm,
        // kobu: 30 ms ≈ Apple "fast pair" recommendation. Cuts macOS
        // discovery / re-pair time from ~10 s to ~1 s.
        interval_min: Duration::from_millis(30),
        interval_max: Duration::from_millis(30),
        ..Default::default()
    };"#;

    if !contents.contains(old_block) {
        panic!(
            "kobu: expected rmk-{RMK_VERSION} ble/mod.rs advertise_config block missing in {}; \
             upstream may have changed or `patch_rmk_ble_for_macos` did not run first — update firmware/build.rs",
            path.display()
        );
    }
    contents = contents.replace(old_block, new_block);

    contents.push('\n');
    contents.push_str(MARKER);
    contents.push('\n');

    fs::write(&path, contents).unwrap_or_else(|e| {
        panic!("kobu: failed to write {}: {e}", path.display());
    });
}

/// Speed up the split-link handshake by lowering the peripheral's
/// advertising interval from `AdvertisementParameters::default()`
/// (= 160 ms in trouble-host 0.5) to 30 ms.
///
/// The central scans for the peripheral with a 5 s connect timeout per
/// attempt; at 160 ms the peripheral advertises only 6×/s, so a missed
/// first scan window adds another 5 s + 500 ms retry. 30 ms keeps the
/// initial both-halves connection well under a second on a cold boot.
fn patch_rmk_split_peripheral_advertise_fast() {
    const MARKER: &str = "// kobu: split peripheral advertise interval lowered to 30 ms applied";
    const RMK_VERSION: &str = "0.8.2";

    let Some(path) = find_rmk_file(RMK_VERSION, "src/split/ble/peripheral.rs") else {
        return;
    };

    println!("cargo:rerun-if-changed={}", path.display());

    let mut contents = fs::read_to_string(&path).unwrap_or_else(|e| {
        panic!("kobu: failed to read {}: {e}", path.display());
    });

    if contents.contains(MARKER) {
        return;
    }

    // Two identical call sites (directed + undirected advertise); a global
    // replace handles both, and the patched literal is unique to this
    // file so subsequent builds short-circuit on the marker.
    let old_call = "&AdvertisementParameters::default()";
    let new_call = "&AdvertisementParameters { interval_min: Duration::from_millis(30), interval_max: Duration::from_millis(30), ..Default::default() }";

    if !contents.contains(old_call) {
        panic!(
            "kobu: expected `{old_call}` not found in {} — upstream may have changed; \
             update firmware/build.rs::patch_rmk_split_peripheral_advertise_fast",
            path.display()
        );
    }
    contents = contents.replace(old_call, new_call);

    contents.push('\n');
    contents.push_str(MARKER);
    contents.push('\n');

    fs::write(&path, contents).unwrap_or_else(|e| {
        panic!("kobu: failed to write {}: {e}", path.display());
    });
}

/// Cut the wait inside `set_conn_params` from 5 s + 5 s to 1 s + 1 s.
///
/// The upstream sequence "wait 5 s → request 15 ms → wait 5 s → request
/// 7.5 ms" means the host link only reaches its fast 133 Hz target ten
/// seconds after a host connects. Until then the keyboard is connected
/// but pointer / typing feel slower. 1 s + 1 s is still well above the
/// pairing / encryption settle time on macOS / iOS / Linux, but gets the
/// device to "full speed" within ~2 s of a fresh host connection.
fn patch_rmk_conn_params_fast_settling() {
    const MARKER: &str = "// kobu: set_conn_params settling delays shortened to 300 ms applied";
    const RMK_VERSION: &str = "0.8.2";

    let Some(path) = find_rmk_file(RMK_VERSION, "src/ble/mod.rs") else {
        return;
    };

    println!("cargo:rerun-if-changed={}", path.display());

    let mut contents = fs::read_to_string(&path).unwrap_or_else(|e| {
        panic!("kobu: failed to read {}: {e}", path.display());
    });

    if contents.contains(MARKER) {
        return;
    }

    // Anchor the first delay on its distinctive preceding comment so we
    // only retime the two set_conn_params waits, not other unrelated
    // 5-second timers elsewhere in the file.
    let first_old = "    // Wait for 5 seconds before setting connection parameters to avoid connection drop\n    embassy_time::Timer::after_secs(5).await;";
    let first_new = "    // kobu: was 5 s — 300 ms is enough on macOS/iOS/Linux and gets the\n    // device to the fast (7.5 ms) conn interval within ~0.6 s of connect.\n    embassy_time::Timer::after_millis(300).await;";

    // Anchor the second delay on the following distinctive comment line.
    let second_old = "    embassy_time::Timer::after_secs(5).await;\n\n    // Setting the conn param the second time ensures that we have best performance on all platforms";
    let second_new = "    embassy_time::Timer::after_millis(300).await;\n\n    // Setting the conn param the second time ensures that we have best performance on all platforms";

    if !contents.contains(first_old) || !contents.contains(second_old) {
        panic!(
            "kobu: expected rmk-{RMK_VERSION} set_conn_params delay anchors missing in {}; \
             upstream may have changed — update firmware/build.rs::patch_rmk_conn_params_fast_settling",
            path.display()
        );
    }
    contents = contents.replace(first_old, first_new);
    contents = contents.replace(second_old, second_new);

    contents.push('\n');
    contents.push_str(MARKER);
    contents.push('\n');

    fs::write(&path, contents).unwrap_or_else(|e| {
        panic!("kobu: failed to write {}: {e}", path.display());
    });
}

/// Lower the host-link BLE slave latency from 30 to 0 in `set_conn_params`.
///
/// `set_conn_params` (ble/mod.rs) requests `max_latency: 30` in BOTH the
/// 15 ms and 7.5 ms `ConnectParams` stages. A slave latency of 30 lets the
/// keyboard skip up to 30 connection events (~450 ms at 15 ms, ~225 ms at
/// 7.5 ms) when it has nothing queued, which measurably degrades
/// time-to-first-report right after a (re)connect on macOS — part of BUG1's
/// "connected but slow to register" window. `0` forces the peripheral to
/// listen every interval; for a powered keyboard the extra idle current is
/// negligible. Supervision timeout (5 s) stays well within spec at latency 0.
///
/// Only the host link (ble/mod.rs) is touched. The split-link conn params in
/// `split/ble/central.rs` (`max_latency: 30, // 225ms`) are deliberately left
/// alone — those govern split-link power/stability and are a separate call;
/// since they live in a different file this in-file replace cannot reach them.
fn patch_rmk_host_conn_low_latency() {
    const MARKER: &str = "// kobu: host set_conn_params max_latency 30 -> 0 applied";
    const RMK_VERSION: &str = "0.8.2";

    let Some(path) = find_rmk_file(RMK_VERSION, "src/ble/mod.rs") else {
        return;
    };

    println!("cargo:rerun-if-changed={}", path.display());

    let mut contents = fs::read_to_string(&path).unwrap_or_else(|e| {
        panic!("kobu: failed to read {}: {e}", path.display());
    });

    if contents.contains(MARKER) {
        return;
    }

    // Both occurrences live in set_conn_params (the 15 ms and 7.5 ms stages).
    let from = "max_latency: 30,";
    let to = "max_latency: 0,";
    if !contents.contains(from) {
        panic!(
            "kobu: expected `{from}` in rmk-{RMK_VERSION} ble/mod.rs set_conn_params at {}; \
             upstream may have changed — update firmware/build.rs::patch_rmk_host_conn_low_latency",
            path.display()
        );
    }
    contents = contents.replace(from, to);

    contents.push('\n');
    contents.push_str(MARKER);
    contents.push('\n');

    fs::write(&path, contents).unwrap_or_else(|e| {
        panic!("kobu: failed to write {}: {e}", path.display());
    });
}

/// Tighten the periodic CONNECTION_STATE re-sync the central pushes to each
/// peripheral from 3000 ms to 500 ms (split/driver.rs `PeripheralManager`).
///
/// The central tells the peripheral whether the host link is up via
/// `SplitMessage::ConnectionState`, sent once on `PeripheralManager` start and
/// then only on a periodic timer — there is NO event-driven push when the
/// host link actually comes up. So if the split link connects BEFORE the host
/// link (common on a cold boot), the peripheral holds a stale `Disconnected`
/// and drops every right-half key + the MAIN (right-side) trackball until the
/// next periodic re-sync — up to 3 s (part of BUG1). 500 ms caps that
/// staleness at ~0.5 s. Cost: one tiny `SplitMessage` every 0.5 s, negligible
/// on the BLE split link.
fn patch_rmk_split_state_resync_fast() {
    const MARKER: &str = "// kobu: split CONNECTION_STATE resync 3000 -> 500 ms applied";
    const RMK_VERSION: &str = "0.8.2";

    let Some(path) = find_rmk_file(RMK_VERSION, "src/split/driver.rs") else {
        return;
    };

    println!("cargo:rerun-if-changed={}", path.display());

    let mut contents = fs::read_to_string(&path).unwrap_or_else(|e| {
        panic!("kobu: failed to read {}: {e}", path.display());
    });

    if contents.contains(MARKER) {
        return;
    }

    let old_block = r#"            // Calculate the time until the next 3000ms sync
            let elapsed = last_sync_time.elapsed().as_millis();
            let wait_time = if elapsed >= 3000 { 1 } else { 3000 - elapsed };"#;
    let new_block = r#"            // kobu: was 3000 ms. 500 ms caps how long a peripheral can hold a
            // stale CONNECTION_STATE after the host link comes up (right-half
            // keys + main trackball were dead for up to 3 s on boot — BUG1).
            let elapsed = last_sync_time.elapsed().as_millis();
            let wait_time = if elapsed >= 500 { 1 } else { 500 - elapsed };"#;

    if !contents.contains(old_block) {
        panic!(
            "kobu: expected rmk-{RMK_VERSION} split/driver.rs 3000 ms resync block missing in {}; \
             upstream may have changed — update firmware/build.rs::patch_rmk_split_state_resync_fast",
            path.display()
        );
    }
    contents = contents.replace(old_block, new_block);

    contents.push('\n');
    contents.push_str(MARKER);
    contents.push('\n');

    fs::write(&path, contents).unwrap_or_else(|e| {
        panic!("kobu: failed to write {}: {e}", path.display());
    });
}

/// Force BLE-priority on boot regardless of any stale persisted
/// `ConnectionType=Usb` (RMK#157). kobu's `patch_rmk_ble_for_macos` rewrote
/// the *default* to Ble, but that default only applies when storage holds NO
/// ConnectionType — a `Usb` value persisted by an older firmware era survives
/// it and routes the device into the non-self-healing USB-priority dual-mode
/// branch. That branch only comes alive on a USB `configured()` callback or a
/// fresh BLE advertise-accept, so after a power cycle the keyboard is dead on
/// BOTH USB and BLE until the host is re-paired — exactly the reported
/// "works only after re-registering in Bluetooth, dead again after power-off"
/// symptom.
///
/// This patch stores `ConnectionType::Ble` UNCONDITIONALLY right after the
/// load, so a stale stored value can never select that branch again. Safe to
/// ship blind: the BLE-priority branch runs the USB keyboard concurrently
/// while advertising, so both USB and BLE HID stay alive, and kobu exposes no
/// keybinding to deliberately force USB-only mode (nothing regresses).
///
/// Anchors on the controller-event send that immediately follows the
/// connection-type load block. `patch_rmk_ble_for_macos` (which only rewrites
/// the default arm) runs earlier and leaves this anchor intact.
fn patch_rmk_force_ble_conn_type() {
    const MARKER: &str = "// kobu: force CONNECTION_TYPE=Ble on boot applied";
    const RMK_VERSION: &str = "0.8.2";

    let Some(path) = find_rmk_file(RMK_VERSION, "src/ble/mod.rs") else {
        return;
    };

    println!("cargo:rerun-if-changed={}", path.display());

    let mut contents = fs::read_to_string(&path).unwrap_or_else(|e| {
        panic!("kobu: failed to read {}: {e}", path.display());
    });

    if contents.contains(MARKER) {
        return;
    }

    let from = r#"        #[cfg(feature = "controller")]
        send_controller_event_new(ControllerEvent::ConnectionType(CONNECTION_TYPE.load(Ordering::SeqCst)));"#;
    let to = r#"        // kobu: force BLE-priority boot regardless of any stale persisted
        // ConnectionType=Usb (RMK#157). The BLE-priority branch runs the USB
        // keyboard concurrently while advertising, so USB still works; this
        // only prevents the non-self-healing USB-priority branch from being
        // selected by a stale stored value.
        CONNECTION_TYPE.store(ConnectionType::Ble.into(), Ordering::SeqCst);
        #[cfg(feature = "controller")]
        send_controller_event_new(ControllerEvent::ConnectionType(CONNECTION_TYPE.load(Ordering::SeqCst)));"#;

    if !contents.contains(from) {
        panic!(
            "kobu: expected rmk-{RMK_VERSION} ble/mod.rs ConnectionType controller-event anchor missing in {}; \
             upstream may have changed — update firmware/build.rs::patch_rmk_force_ble_conn_type",
            path.display()
        );
    }
    contents = contents.replace(from, to);

    contents.push('\n');
    contents.push_str(MARKER);
    contents.push('\n');

    fs::write(&path, contents).unwrap_or_else(|e| {
        panic!("kobu: failed to write {}: {e}", path.display());
    });
}
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
