s-katada/kobu/v2/firmware/rmk/src/central.rs

#![no_main]
#![no_std]

mod battery_source;
mod config;
mod set_token;
mod status_led;
mod trackball;

use rmk::macros::rmk_central;

#[rmk_central]
mod keyboard_central {
    use crate::battery_source::{CentralBatteryTagger, KobuBatterySourceTap};
    use crate::status_led::StatusLedController;
    use crate::trackball::{
        AxisRelabel, PeriphScrollRelabel, PointerProcessor, ScrollProcessor, run_auto_mouse_layer,
        run_input_gate_central,
    };

    // Status LED controller declared via the `rmk_macro` controller
    // attribute. The macro extracts the function body and emits
    // `let mut status_led = { <body> };` into the entry scope before our
    // override runs, so `status_led` is available below when we wire it
    // into the task join.
    //
    // The R/G/B pins are claimed from `p` here — they're not registered
    // as static `[[output]]` pins in keyboard.toml so `p.P0_26`,
    // `p.P0_30`, and `p.P0_06` are still owned by the peripherals struct
    // at this point. Uses `#[controller(poll)]` so the controller's
    // `update()` tick can deterministically expire the boot-battery /
    // connect-flash windows and poll the host-connect edge.
    #[controller(poll)]
    fn status_led() {
        use ::embassy_nrf::gpio::{Level, Output, OutputDrive};
        // HighDrive (2026-08-13): green/blue have ~1 V higher forward voltage
        // than red; at Standard drive their sink current can be too small to
        // light visibly ("red works, green/blue dark" field report).
        let red = Output::new(p.P0_26, Level::High, OutputDrive::HighDrive);
        let green = Output::new(p.P0_30, Level::High, OutputDrive::HighDrive);
        let blue = Output::new(p.P0_06, Level::High, OutputDrive::HighDrive);
        StatusLedController::new(red, green, blue)
    }

    // Override the macro-generated entry so we can:
    //   1. wrap the central-local PMW3610 with `AxisRelabel` (X→H, Y→V),
    //   2. run `[PeriphScrollRelabel, ScrollProcessor, PointerProcessor,
    //      battery_processor]` as the processor chain (PeriphScrollRelabel
    //      remaps the right ball to scroll while H+J is held), and
    //   3. spawn `battery_color_led` alongside everything else.
    //
    // Variable bindings still in scope from the macro at this point:
    //   * `left_device`, `left_processor`      — central-local PMW3610
    //   * `right_processor`                     — placeholder for the
    //                                             peripheral PMW3610
    //   * `adc_device`, `battery_processor`     — SAADC + battery decoder
    //                                             (from `[ble]` config)
    //   * `status_led`                          — our controller (above)
    //   * `matrix`, `keyboard`, `keymap`,
    //     `storage`, `driver`, `stack`,
    //     `rmk_config`, `peripheral_addrs`      — boilerplate from the macro
    #[Overwritten(entry)]
    async fn rmk_entry() {
        use ::rmk::controller::PollingController;
        use ::rmk::input_device::Runnable;

        // Discard the macro-generated default Pmw3610Processor bindings.
        let _ = left_processor;
        let _ = right_processor;

        // Multi-set independence: stamp THIS set's split-adv token before
        // scan/advertise starts, and override the Mac-facing BLE/USB name+PID
        // so two sets show up as `kobu2 octopus` vs `kobu2 squid` (set_token.rs).
        crate::set_token::apply_split_set_token();
        let mut rmk_config = rmk_config;
        crate::set_token::apply_host_identity(&mut rmk_config);

        let mut left_relabeled = AxisRelabel::new(left_device);
        let mut periph_scroll_relabel = PeriphScrollRelabel::new(&keymap);
        let mut scroll_processor = ScrollProcessor::new(&keymap);
        let mut pointer_processor = PointerProcessor::new(&keymap);

        // Wrap the macro-generated `adc_device` so its `Event::Battery`
        // samples arrive with the kobu source-tag bit set. The upstream
        // `BatteryProcessor` never sees the bit because
        // `KobuBatterySourceTap` (chain head) strips it before forwarding
        // central samples downstream. The tap also mirrors each side's
        // percentage into `rmk::input_device::battery::KOBU_*_BATTERY_PERCENT`
        // so the patched Via Custom Get handler can answer kobu-config polls.
        let mut tagged_adc = CentralBatteryTagger::new(adc_device);
        let mut battery_source_tap = KobuBatterySourceTap::new(&keymap);

        // Pointer-CPI multiplier at boot. Lowered 2500 (2.5×) → 1500 (1.5×):
        // 2.5× made the smallest cursor step ~2-3px, which fought precise
        // click-aim ("微調整が厳しい"). 1.5× gives finer granularity while macOS
        // pointer acceleration still makes fast flicks fast. The dominant
        // "もっさり" lag was the split-link slave latency (fixed separately in
        // build.rs::patch_rmk_split_conn_low_latency), not the CPI. Applied in
        // trackball.rs::run_pointer_flush and live-tunable from kobu-config
        // (Via Custom Channel 0xC0 id 0x01, range 0.2×–3.2×) so it can be
        // re-dialed without a reflash. Re-asserted every boot (no persistence).
        ::rmk::input_device::battery::KOBU_TRACKBALL_CPI
            .store(1500, ::core::sync::atomic::Ordering::Relaxed);

        ::rmk::embassy_futures::join::join(
            ::rmk::embassy_futures::join::join(
                ::rmk::embassy_futures::join::join(
                    ::rmk::embassy_futures::join::join(
                        ::rmk::embassy_futures::join::join(
                            ::rmk::embassy_futures::join::join(
                                ::rmk::run_devices!(
                                    (left_relabeled, tagged_adc, matrix) => ::rmk::channel::EVENT_CHANNEL,
                                ),
                                keyboard.run(),
                            ),
                            ::rmk::run_rmk(&keymap, driver, &stack, &mut storage, rmk_config),
                        ),
                        ::rmk::run_processor_chain!(
                            ::rmk::channel::EVENT_CHANNEL => [battery_source_tap, periph_scroll_relabel, scroll_processor, pointer_processor, battery_processor],
                        ),
                    ),
                    ::rmk::split::central::run_peripheral_manager::<4, 5, 0, 5, _>(
                        0,
                        &peripheral_addrs,
                        &stack,
                    ),
                ),
                ::rmk::split::ble::central::scan_peripherals(&stack, &peripheral_addrs),
            ),
            ::rmk::embassy_futures::join::join(
                ::rmk::embassy_futures::join::join(
                    status_led.polling_loop(),
                    // Round 8 boot-trackball wedge fix: hold the PMW3610
                    // pipeline (both halves) OFF until the host link is READY
                    // (BLE-encrypted or USB), so motion can't stall the Mac
                    // SMP/encryption bring-up. Drives KOBU_INPUT_GATED +
                    // KOBU_HOST_READY (→ peripheral via HostReady). See
                    // src/trackball.rs::run_input_gate_central.
                    //
                    // Pointer reports are now emitted INLINE by PointerProcessor
                    // (like ScrollProcessor), so the old run_pointer_flush drain
                    // task is gone — this leaf used to be join(flush, gate).
                    run_input_gate_central(),
                ),
                // Auto mouse layer: switch to layer 4 while the right-half
                // trackball is moving, fall back after an idle window. Shares
                // `keymap` with run_rmk/keyboard; borrows are single-statement
                // and never held across an await. See src/trackball.rs.
                run_auto_mouse_layer(&keymap),
            ),
        )
        .await;
    }
}
